clawdbotatg/clawd-pico-case/renders/plan/photo-stick-tilt.png

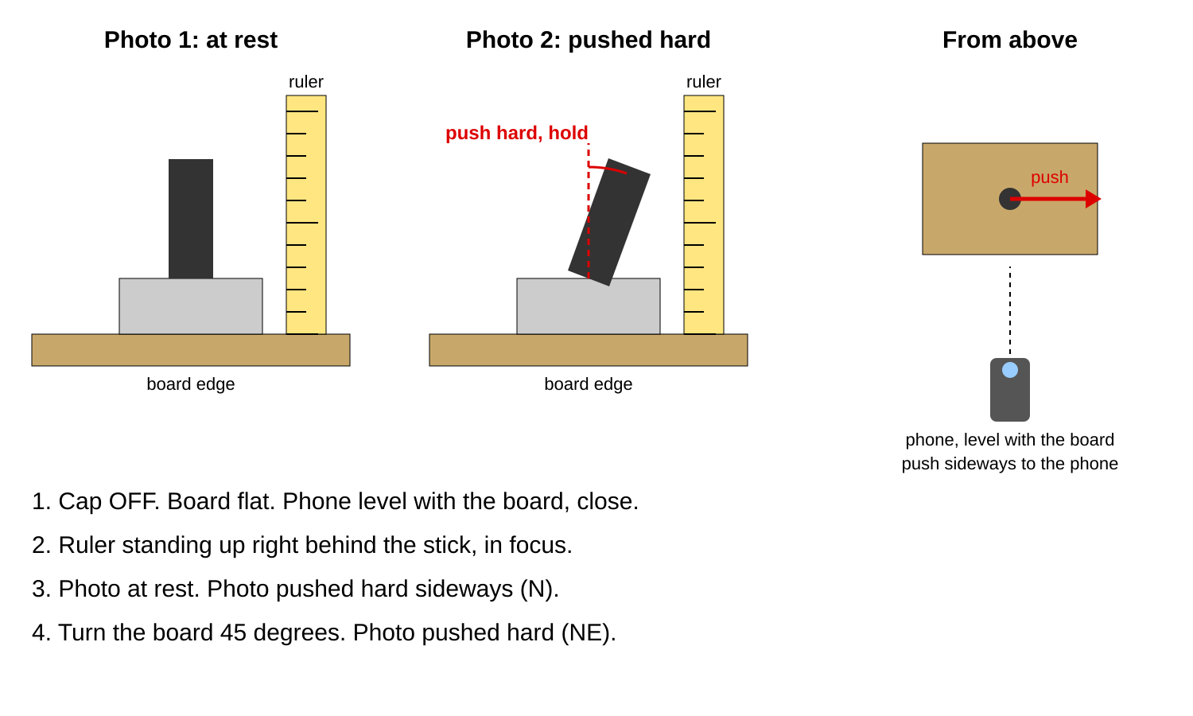
renders/plan/photo-stick-tilt.png
