clawdbotatg/clawd-pico-case/renders/r4-preview.png

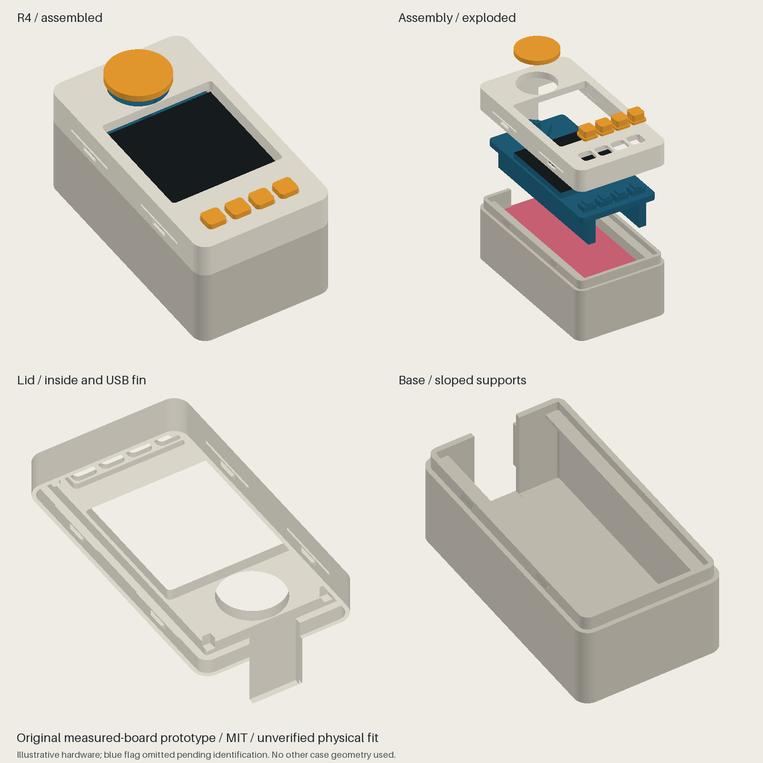
renders/r4-preview.png
