clawdbotatg/clawd-pico-case/renders/v3-browser.png

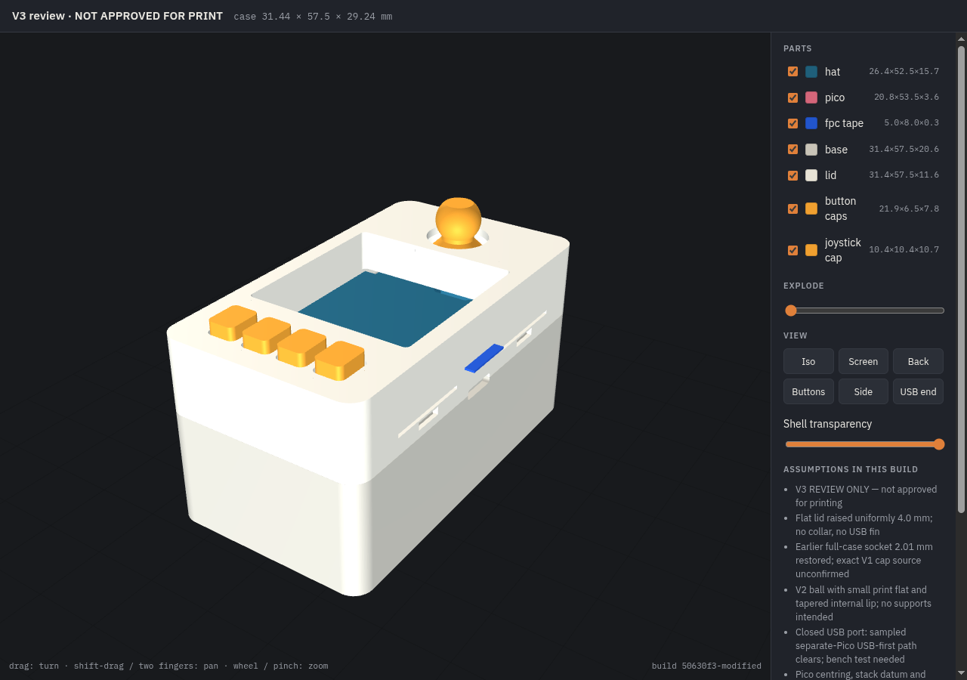
renders/v3-browser.png
