clawdbotatg/clawd-pico-case/renders/v3-low/browser.png

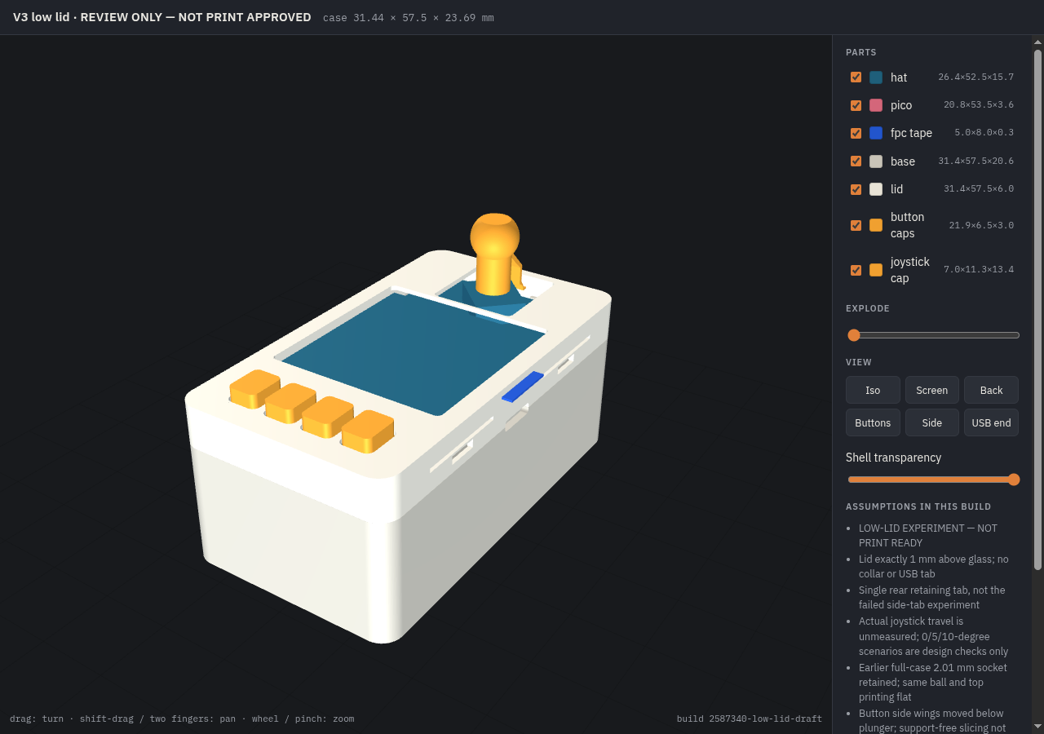
renders/v3-low/browser.png
