clawdbotatg/clawd-pico-case/stl/s2-tight-base/s2-base-and-four-buttons.stl

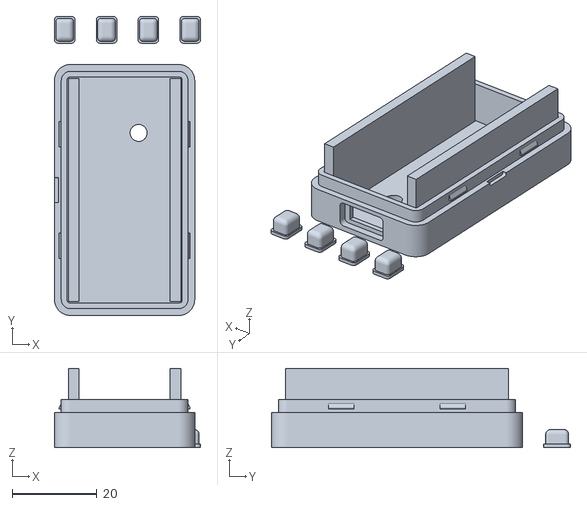
[picture p18: CAD file, 2026-09-25]
stl/s2-tight-base/s2-base-and-four-buttons.stl
34.4 x 70.4 x 18.7
