clawdbotatg/clawd-pico-case/stl/test/j24-fit/joystick-j24-fit-3.stl

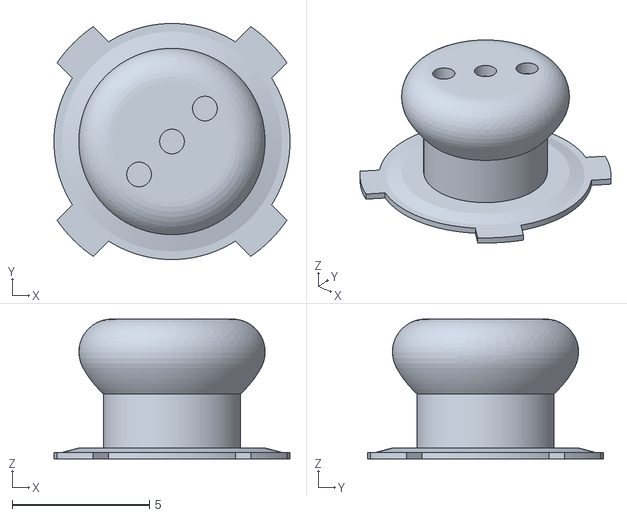
[picture p20: CAD file, 2026-10-02]
stl/test/j24-fit/joystick-j24-fit-3.stl
8.60 x 8.60 x 5.10
