clawdbotatg/clawd-pico-case/stl/test/j24/joystick-j24-B.stl

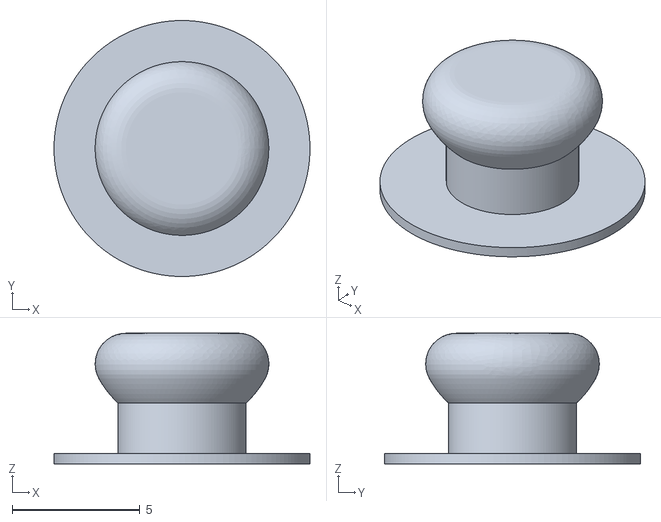
[picture p21: CAD file, 2026-10-02]
stl/test/j24/joystick-j24-B.stl
10.0 x 10.00 x 5.10
