clawdbotatg/clawd-pico-case/stl/test/v1.9/lid-v1.9-test-face-down.stl

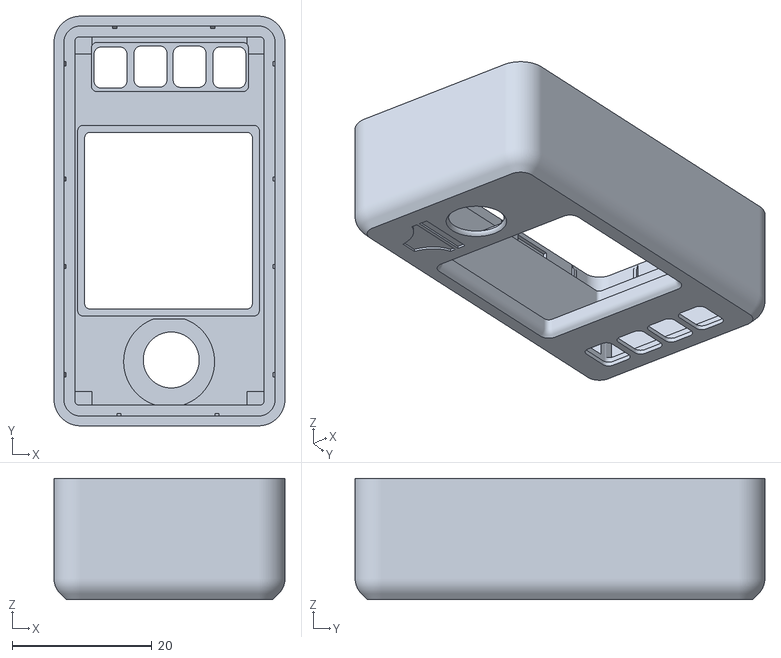
[picture p22: CAD file, 2026-10-02]
stl/test/v1.9/lid-v1.9-test-face-down.stl
33.0 x 58.6 x 17.4
