clawdbotatg/clawd-pico-case/stl/v3-flat/v3-flat-lid-face-down.stl

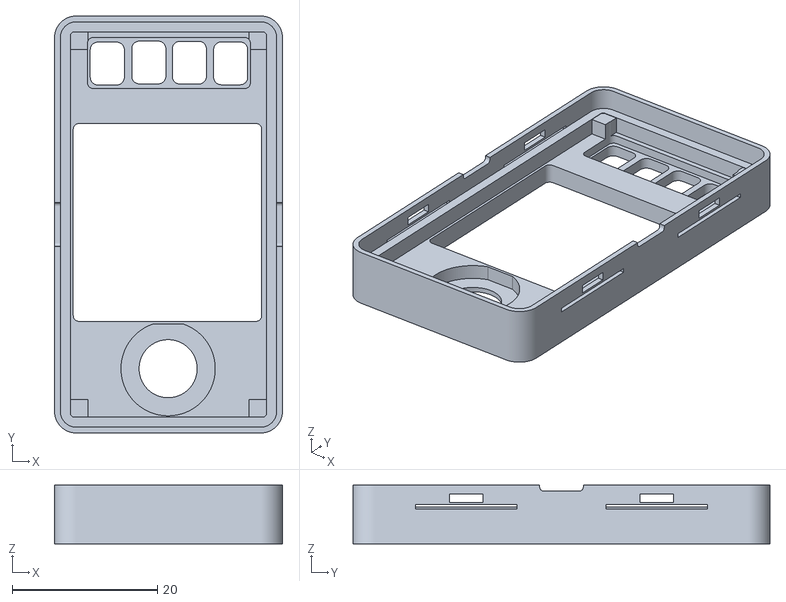
[picture p23: CAD file, 2026-09-25]
stl/v3-flat/v3-flat-lid-face-down.stl
31.4 x 57.5 x 8.10
