clawdbotatg/clawd-pico-case/stl/button_caps.stl

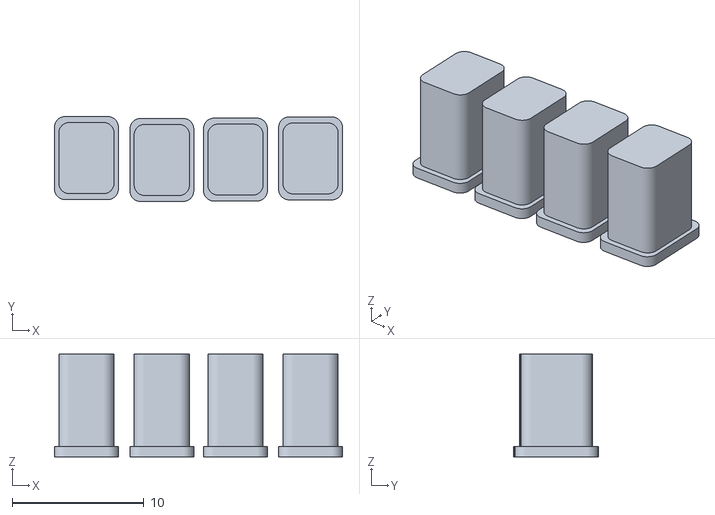
[picture p24: CAD file, 2026-09-25]
stl/button_caps.stl
21.9 x 6.44 x 7.79
