clawdbotatg/clawd-pico-case/stl/current/joystick.stl

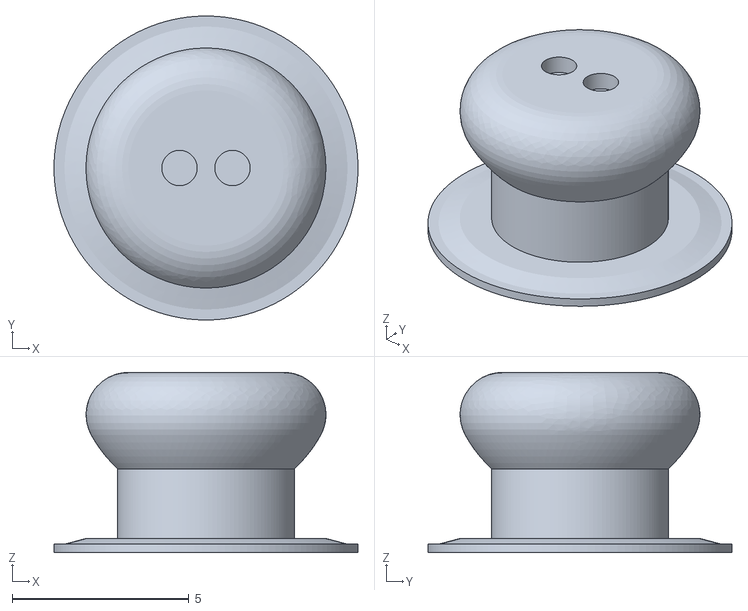
[picture p25: CAD file, 2026-09-30]
stl/current/joystick.stl
8.60 x 8.60 x 5.10
