clawdbotatg/clawd-pico-case/stl/j3-low-lid/lid-and-joystick.stl

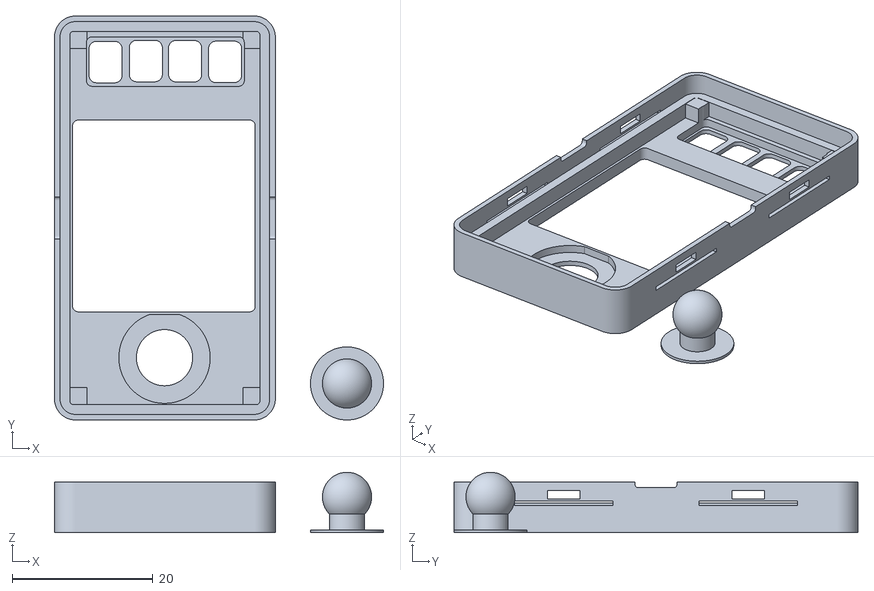
[picture p26: CAD file, 2026-09-25]
stl/j3-low-lid/lid-and-joystick.stl
46.8 x 57.5 x 8.60
