clawdbotatg/clawd-pico-case/stl/joystick-j1/joystick-cap.stl

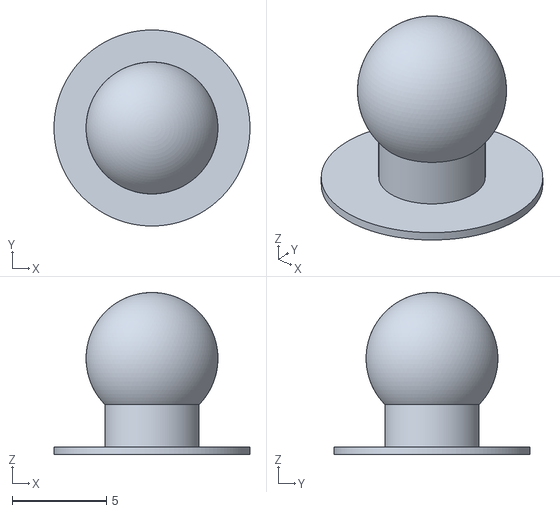
[picture p27: CAD file, 2026-09-25]
stl/joystick-j1/joystick-cap.stl
10.4 x 10.4 x 8.60
