clawdbotatg/clawd-pico-case/stl/l2-j2/l2-lid-and-j2.stl

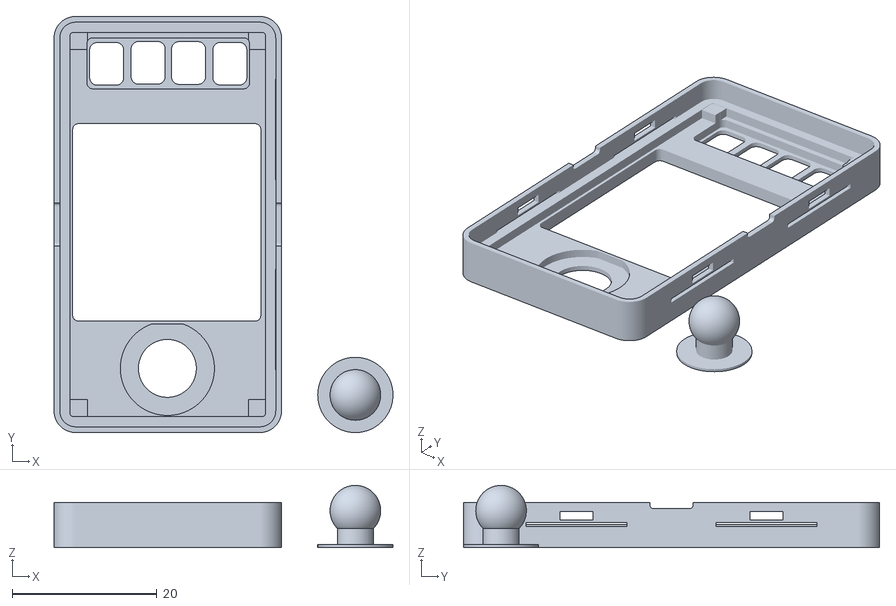
[picture p28: CAD file, 2026-09-25]
stl/l2-j2/l2-lid-and-j2.stl
46.8 x 57.5 x 8.60
