clawdbotatg/clawd-pico-case/stl/s1-full-print/button-1.stl

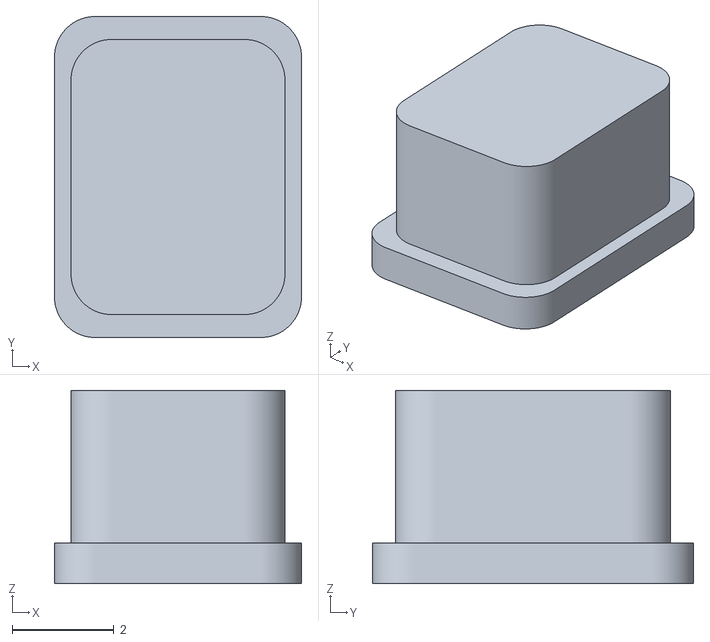
[picture p29: CAD file, 2026-09-25]
stl/s1-full-print/button-1.stl
4.85 x 6.30 x 3.79
