clawdbotatg/clawd-pico-case/stl/test/j24-fit/joystick-j24-fit-plate.stl

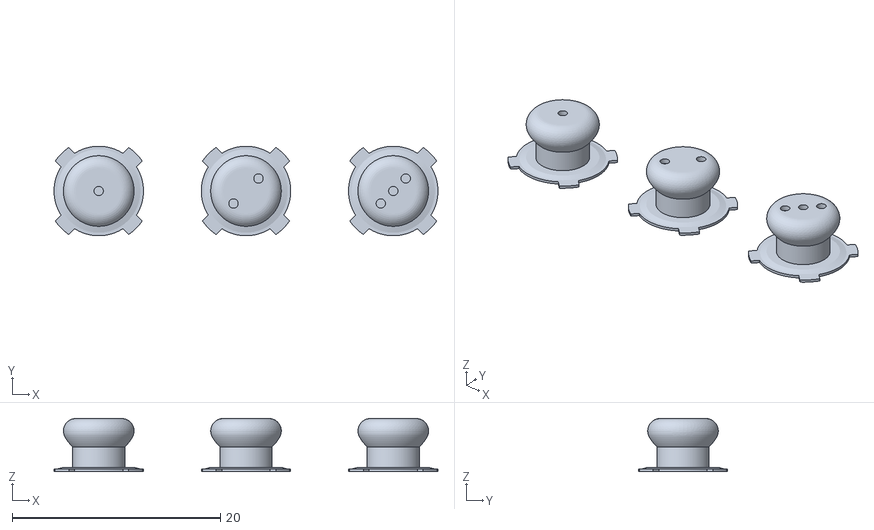
[picture p31: CAD file, 2026-10-02]
stl/test/j24-fit/joystick-j24-fit-plate.stl
36.9 x 8.60 x 5.10
