clawdbotatg/clawd-pico-case/stl/test/v1.9/logo-inlay-face-down.stl

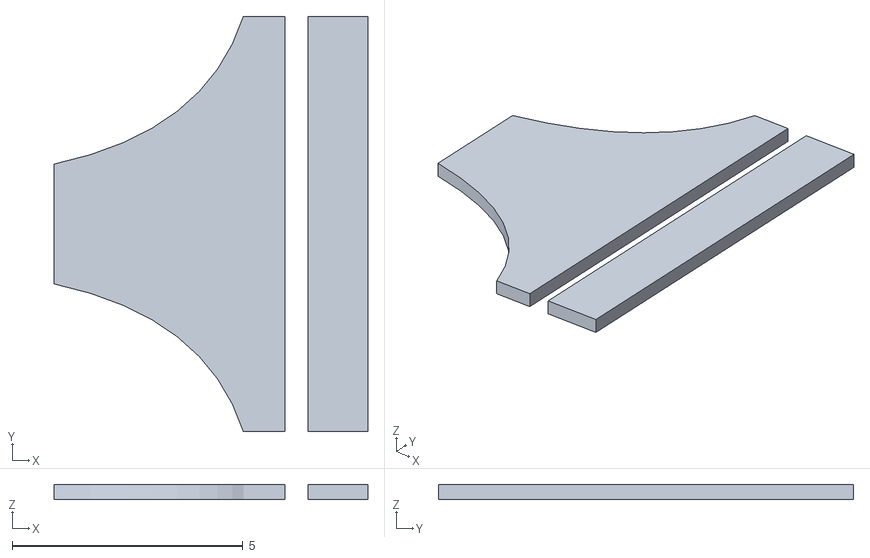
[picture p32: CAD file, 2026-10-02]
stl/test/v1.9/logo-inlay-face-down.stl
6.80 x 9.00 x 0.32
