clawdbotatg/clawd-pico-case/stl/base.stl

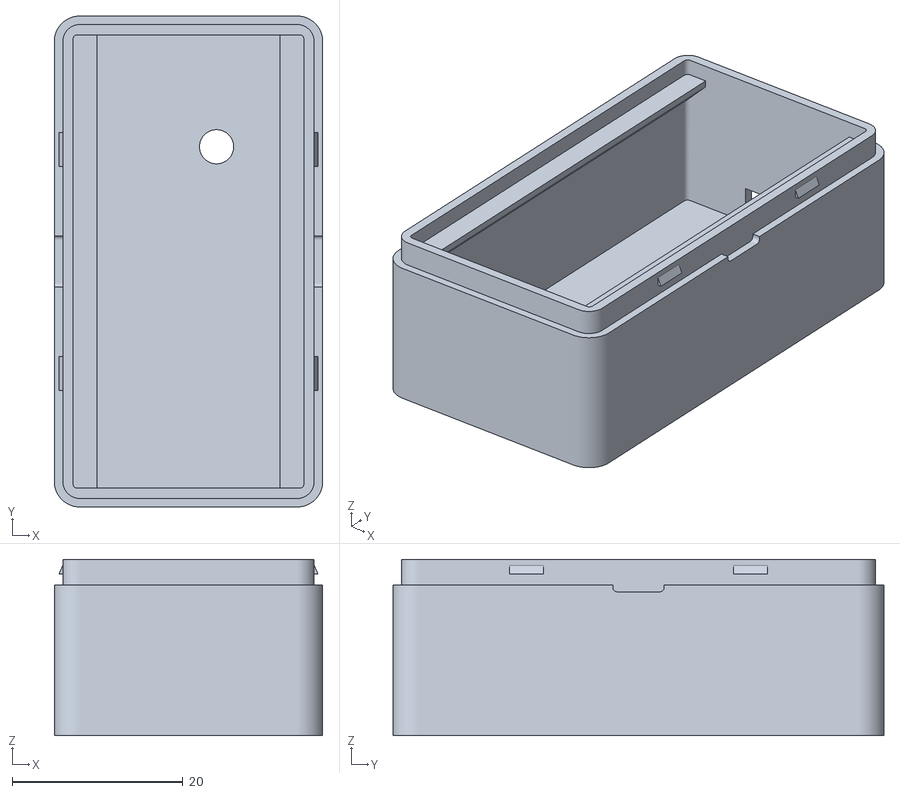
[picture p33: CAD file, 2026-09-25]
stl/base.stl
31.4 x 57.5 x 20.6
