clawdbotatg/clawd-pico-case/stl/current/lid.stl

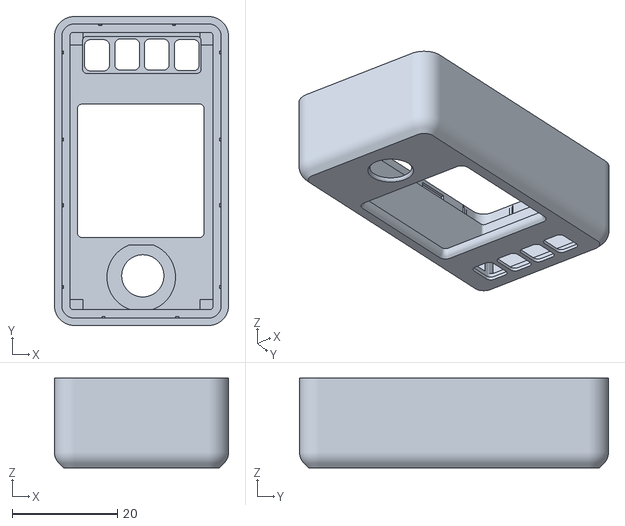
[picture p34: CAD file, 2026-09-27]
stl/current/lid.stl
33.0 x 58.6 x 17.1
