clawdbotatg/clawd-pico-case/stl/j3-low-lid/joystick-j3.stl

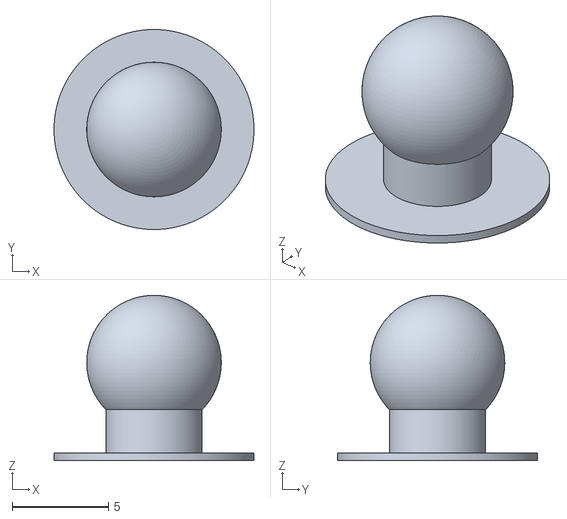
[picture p35: CAD file, 2026-09-25]
stl/j3-low-lid/joystick-j3.stl
10.4 x 10.4 x 8.60
