clawdbotatg/clawd-pico-case/stl/joystick-j1/lid-gauge.stl

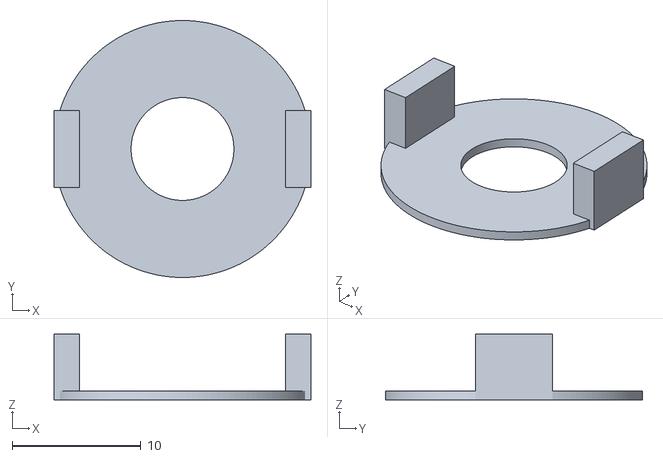
[picture p36: CAD file, 2026-09-25]
stl/joystick-j1/lid-gauge.stl
20.0 x 20.0 x 5.10
