clawdbotatg/clawd-pico-case/stl/test/aw-reset-v3/reset-v3-3-notch.stl

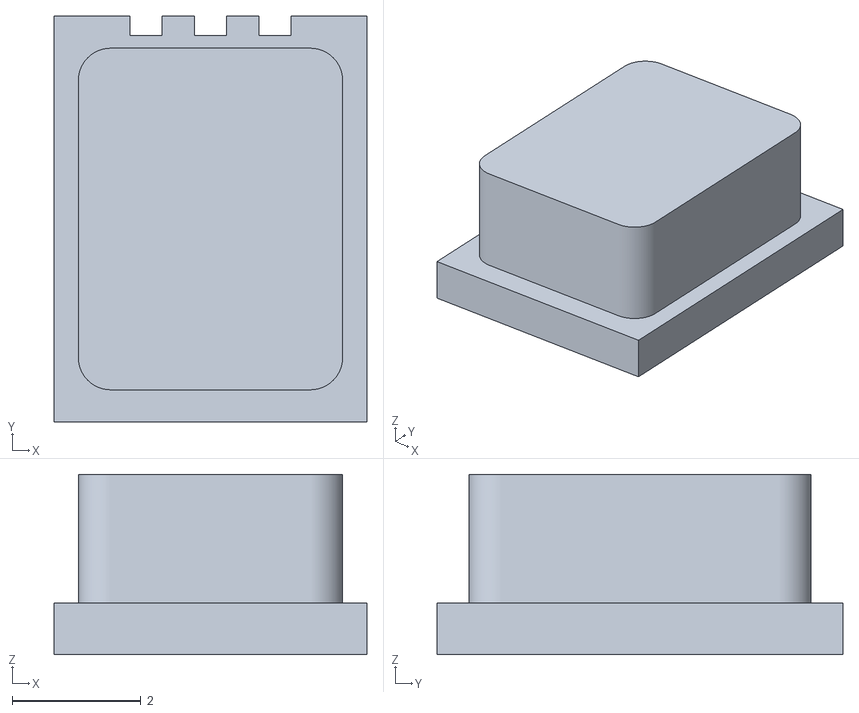
[picture p37: CAD file, 2026-10-09]
stl/test/aw-reset-v3/reset-v3-3-notch.stl
4.85 x 6.30 x 2.80
