clawdbotatg/clawd-pico-case/stl/v3-fit/v3-shells-only.stl

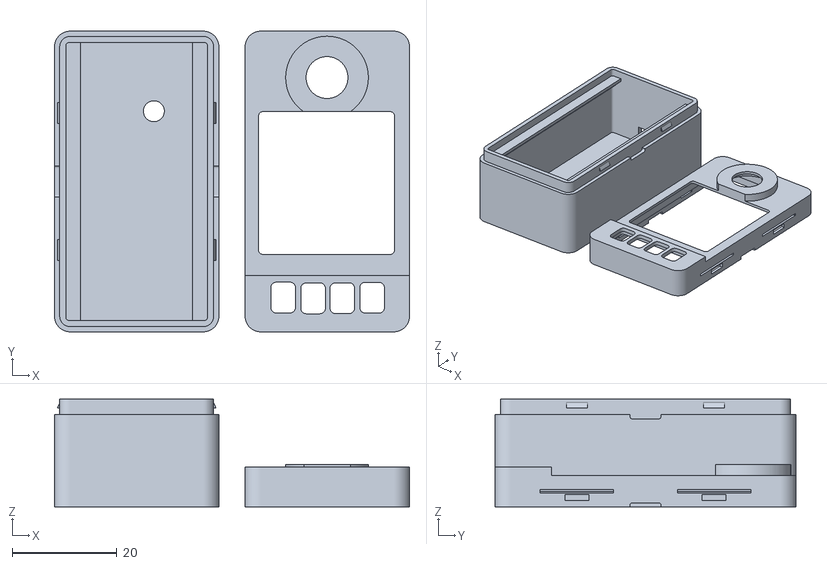
[picture p38: CAD file, 2026-09-25]
stl/v3-fit/v3-shells-only.stl
67.9 x 57.5 x 20.6
