clawdbotatg/clawd-pico-case/stl/current/button.stl

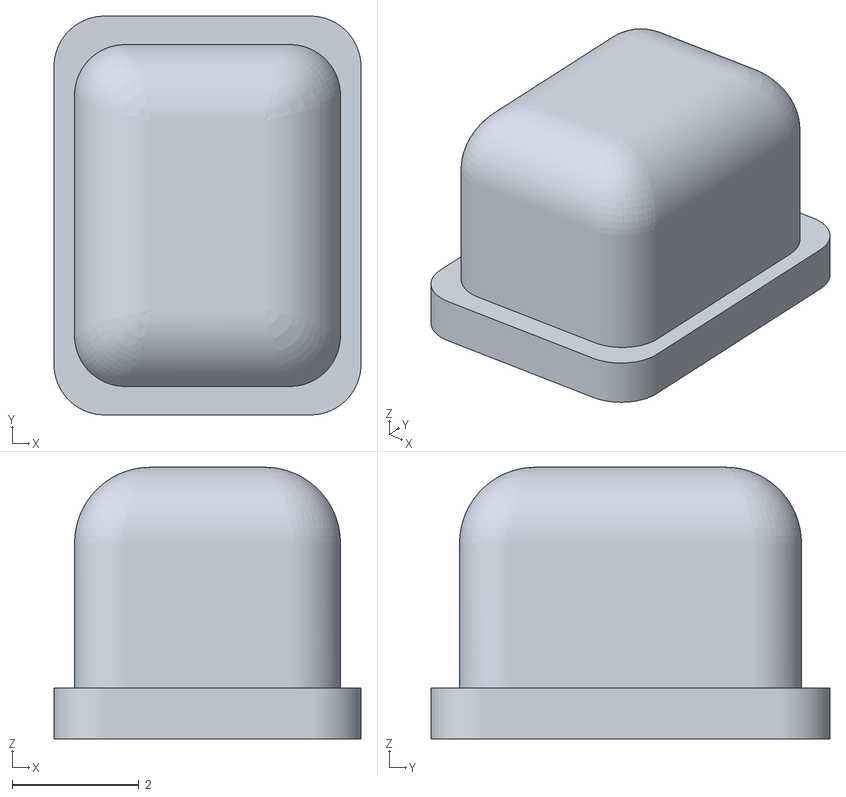
[picture p39: CAD file, 2026-09-25]
stl/current/button.stl
4.85 x 6.30 x 4.29
