clawdbotatg/clawd-pico-case/stl/lid.stl

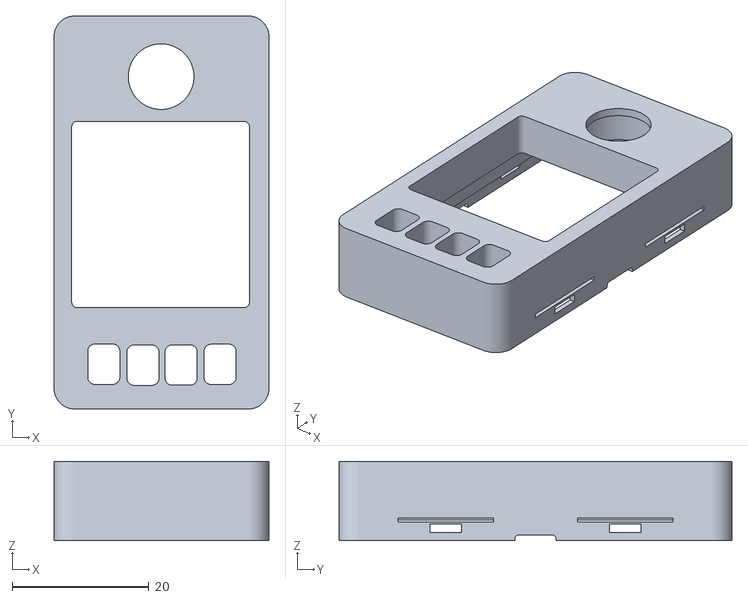
[picture p40: CAD file, 2026-09-25]
stl/lid.stl
31.4 x 57.5 x 11.6
