clawdbotatg/clawd-pico-case/stl/pico.stl

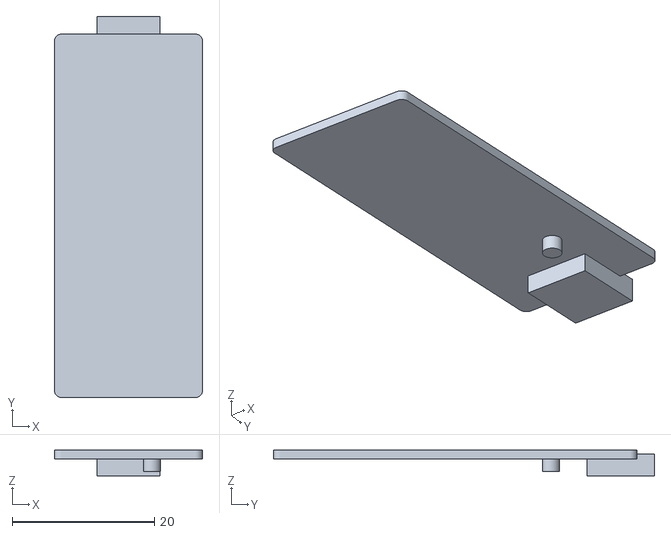
[picture p41: CAD file, 2026-09-25]
stl/pico.stl
20.8 x 53.5 x 3.64
