clawdbotatg/clawd-pico-case/stl/hat.stl

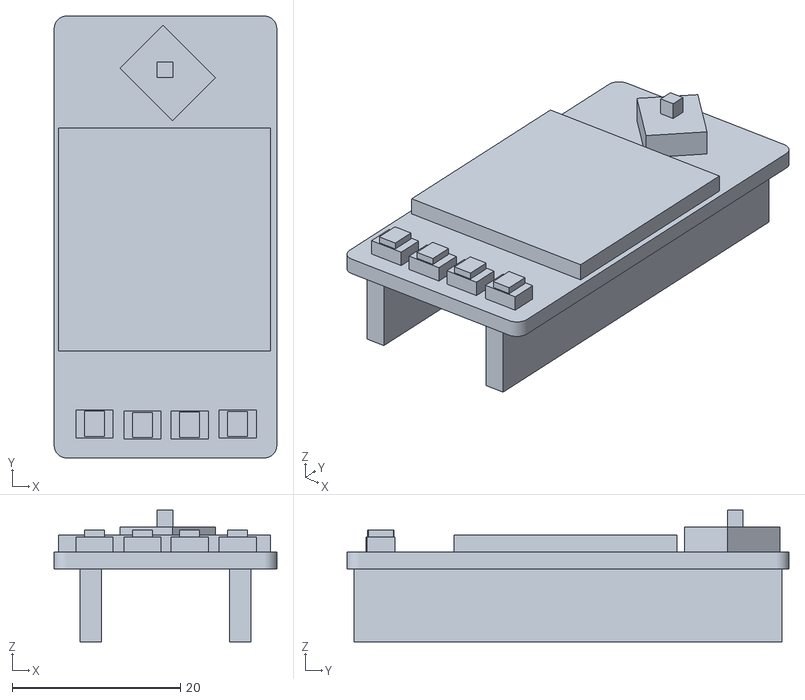
[picture p42: CAD file, 2026-09-25]
stl/hat.stl
26.4 x 52.5 x 15.7
