clawdbotatg/clawd-pico-case/stl/fpc_tape.stl

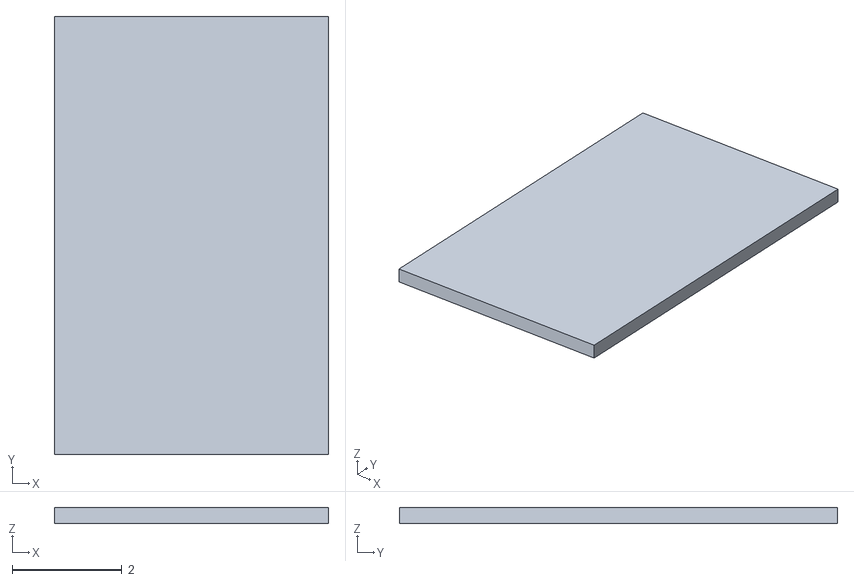
[picture p43: CAD file, 2026-09-25]
stl/fpc_tape.stl
5.00 x 8.00 x 0.3
