clawdbotatg/clawd-pico-case/prints/2026-09-25-v1.3-lid-petg.md

# v1.3 lid — white PETG

Austin approves the short-USB-end approach ("this is the way") and asks for
the lid in white PETG (bay 2). It replaces the v1.1 lip lid. The lid's USB-C
end wall is 0.5 mm further in, and there is no lip.

Source ccf3351, `stl/v1.3/lid-face-down.stl`, SHA256
`eddf98bfa6c56df3ee43523b8e432f1ef07ad944e9342fcf71011e93c7d7c223`.
33.04 × 58.60 × 16.56 mm. PETG, 0.16 mm, 4 walls, no supports, no raft,
face down.

Sent to the HTTP inbox as `20260925-205019-lid-face-down` with a GO (queue
after any running job). Status: new. Print start unconfirmed.

The lid matches only the v1.3 base: the case ends are 0.5 mm shorter, so it
will not sit flush on a v1.0 or v1.1 base.
