clawdbotatg/clawd-pico-case/prints/2026-09-25-v1.0-caps-petg.md

# v1.0 joystick + two buttons — gray PETG

Austin asks for the joystick cap and two button caps only, in gray PETG from
AMS bay 3. The parts are unchanged v1.0 (J2 joystick, S2 buttons 1–2; all
four buttons are identical). `cad/v1_caps_plate.py` lays them out.

File `stl/v1.0/v1.0-joystick-and-two-buttons.stl`, SHA256
`be922982d110cce2e86359edca736fd24d92bfe1885c461e6eff6b5294474495`.
30.10 × 10.40 × 8.60 mm. PETG, 0.16 mm, 4 walls, no supports, no raft,
flanges down.

Sent to the HTTP inbox as `20260925-190845-v1.0-joystick-and-two-buttons` with
an explicit GO (queue after any running job). Status: new. Print start
unconfirmed.
