clawdbotatg/clawd-pico-case/prints/2026-09-25-s2-base-buttons.md

# S2 replacement base + four buttons

Austin requests next iteration for tighter S1 closure and more distinct
rounded/taller buttons; minimize shell reprints. Print FIVE pieces only.
Keep existing S1 lid and J2 joystick. No change to case height/hole alignment.

File stl/s2-tight-base/s2-base-and-four-buttons.stl. Base floor DOWN/cavity UP,
four buttons flange DOWN. PLA available color,0.16mm,4walls, supports OFF,
raft OFF. No lid/joystick/PETG or extra parts.

New flat catch underside has short0.50mm overhang: inspect slicing along with
USB bridge, rails and rounded cap tops. Hold/report if support-free printing
is not viable; no silent geometry/orientation/support changes. Confirm bed
clear by camera, wait if busy, start watcher. Let plate cool before removal.

36 checks pass: same lid, base changes only at catches, seated clearance,
reduced nominal play, button interfaces/travel/retention and five-part plate.
Fit/force untested. Try closing gently, then hold by top and check for hanging
base or rattle. Test button feel/full travel and pry-notch release; do not
force if fit is too tight.0.04mm nominal play is not an FDM accuracy claim.

Source cc52b45 sent via HTTP inbox as
`20260925-161927-s2-base-and-four-buttons`.
Server confirms34.40×70.40×18.67mm, fits bed, matching SHA256:
`044036e3313a87cc659227e269e47603cd21a9ca204dde046f40b6c65acd14ca`.
Explicit GO accepted; initial status new, actual start unconfirmed.
Austin notified by inbox. Browser render/controls test also passed.

## Result

Printed and assembled with the S1 lid and J2. Austin: "This works. This is
good." The snap and the button feel are accepted. Three 0.25 mm nudges
remain (joystick hole, USB-C height, reset hole); they went into
[V1.0](../RELEASE-v1.0.md) and were not reprinted in PLA.
