clawdbotatg/clawd-pico-case/prints/2026-09-25-s1-full-case.md

# S1 full case — 2026-09-25

Austin approved interactive model and explicitly requested full set now.
Seven pieces: S1 lid/base, one unchanged J2 joystick, four unchanged V2
buttons. Approved S1 shell source 5c6f7ab. Original review artifacts retained.

Plate stl/s1-full-print/s1-full-case-seven-parts.stl. Individual STLs beside it.
Lid exterior FACE DOWN, base floor DOWN/cavity UP, all caps flange DOWN.
PLA available color, 0.16 mm, 4 walls for stronger shells, supports OFF,
raft OFF. No extra parts, no scaling or alternate orientations.

Operator must preview all seven pieces, thin control roofs, hidden catches,
USB bridge, support rails and cap sockets. Confirm bed clear by camera,
wait if busy, start print watcher. Hold/report if support-free slicing fails;
do not add supports or flip lid. Strength/joint force/physical fit untested.
Cool plate before removal; test assembly gently without forcing hardware.

Sent packaging source d57302f via HTTP inbox:
`20260925-145729-s1-full-case-seven-parts`.
Server confirms 71.08 × 74.50 × 18.67 mm, fits bed, matching SHA256
`185554416fa7e59e3f17f83e36e086e3585ead93e732c9803bf214de4090b9d1`.
14 packaging checks pass, including exact shell/J2 file matches, seven solids,
all parts on bed and separated. Explicit GO accepted; initial status new.
Austin notified by inbox. Actual print start not yet confirmed.
## User-supplied production photograph

Austin subsequently supplies IMG_0839 showing shells and controls on printer
bed. Archived with provenance/hashes at [s1-photos](s1-photos/README.md).
This supports physical production of the iteration; no exact completion time,
successful assembly, or functional fit is inferred from the photograph.
## Assembled fit feedback

Austin reports S1 very close. Holding top lets base hang approximately 0.25 mm;
closure too easy/loose. Buttons feel indistinct/close under finger. Requests
one-half reprint if possible and taller rounded button tops. Assembled photo
IMG_0840 archived in s1-photos, duplicate uploads saved once. Next S2 trial
keeps lid/J2 and replaces base catches plus four button tops.
