clawdbotatg/clawd-pico-case/prints/2026-09-25-l3-shifted-hole.md

# L3 — lid only alignment correction

Restore L1 face z4.20 and joystick underside z3.50 after L2 closure failure.
Only opening moves 1.00 mm toward LCD, diameter stays 8 mm. Pocket unchanged.
Reuse existing base/buttons/J2. User-owned IMG_0831/0830/0829 provide direction;
amount follows explicit request. No physical fit guarantee.

Print stl/l3-shifted-hole/l3-lid-face-down.stl, one lid FACE DOWN as exported.
PLA available color, 0.16 mm, 3 walls, supports OFF, raft OFF. No other parts.
Operator previews thin roofs/snap bridges, confirms bed clear by camera,
waits if busy and starts watcher. No orientation changes or added supports.
Source e082ac8 sent via HTTP inbox: `20260925-140900-l3-lid-face-down`.
Server confirms 31.44 × 57.50 × 7.20 mm, fits bed, matching SHA256
`36425a396bdc524a374d7511813842214572617c2d0387cb5ad942edbf78c358`.
Explicit GO accepted; initial status new. Print start unconfirmed.
Nine geometry checks and browser interaction test passed. Austin notified
by inbox. No physical fit result yet.
## Physical feedback

Austin reports 1 mm shift overshot; IMG_0833 latest versus IMG_0832 prior.
Next trial should move halfway back and slightly photo-up.
