clawdbotatg/clawd-pico-case/prints/2026-09-25-l2-j2.md

# L2 lid and unchanged J2 — 2026-09-25

Austin explicitly authorizes this uncertain-fit trial. L1 roof and underside
lowered 1.00 mm with thickness retained; unchanged mating skirt, base, buttons.
J2 joystick reprint byte-identical, not rejected J3.

File stl/l2-j2/l2-lid-and-j2.stl. Exactly one lid FACE DOWN and one joystick
flange DOWN, socket mouth at bed. PLA available color, 0.16 mm, 3 walls,
supports OFF, raft OFF. No other parts. Inspect bridges, thin roof, socket and
flange in slicer; camera-confirm bed clear, wait if busy, start watcher.

Seven structural checks pass. Hat/button CAD overlaps explicitly recorded
in renders/l2-j2/validation.json. Physical fit is NOT confirmed; user requests
the print anyway. Test gently, never force the lid onto hardware.

Sent source c7a0315 via HTTP inbox as `20260925-133723-l2-lid-and-j2`.
Server confirms 46.84 × 57.50 × 8.60 mm, fits bed, matching SHA256:
`7777ba5cc1b18bc5eb67cdedb275aa89db74edf8472d4698a71c1621fcf4f692`.
Explicit GO accepted. Initial status new; print start not confirmed.
Austin notified by inbox. No physical fit result yet.
## Physical feedback

Austin reports case will not close with joystick and buttons installed.
L2 rejected; restore L1 height for next lid. Keep J2 joystick.
