clawdbotatg/clawd-pico-case/prints/2026-09-25-j3-low-lid.md

# J3 joystick / L1 lowered lid — 2026-09-25

Authorized by Austin after J2 socket was too tight. Round cavity 3.50 mm
diameter × 1.10 mm deep; unchanged square 2.01 × 2.00 mm beyond it.
Whole flat lid lowered 0.90 mm. Reuse printed V3 base and V2 buttons.

File: stl/j3-low-lid/lid-and-joystick.stl. Two solids, lid exterior FACE DOWN,
joystick flange DOWN, socket open at bed. PLA available color, 0.16 mm,
3 walls, supports OFF, raft OFF. No other parts.

Operator must inspect thin 0.64 mm button roof, snap bridges, socket steps,
ball overhang and flange before printing; camera-confirm clear bed; wait if
busy; start watcher. Do not change orientation or add supports. Hold/report
if support-free slicing is not viable.

18 geometry checks pass; seating and motion remain unverified. Try fitting
gently, check all joystick directions and press, then assess next lowering.
Sent corrected geometry afbbed9 via HTTP inbox:
`20260925-130413-lid-and-joystick`. Server confirmed 46.84 × 57.50 × 8.60 mm,
fits bed; SHA256 matches local:
`48fbb2ea6573a903808038da437028feda14a8ace97b4a049d66f5b4a0569405`.
Initial status `new`. Explicit GO sent. Print start not confirmed.
Austin notified by inbox. No physical results yet.
