clawdbotatg/clawd-pico-case/prints/2026-09-25-joystick-j2.md

# J2 stepped-socket cap — submitted, start unconfirmed

Source53632f9 pushed before HTTP submission. Drop
`20260925-124312-joystick-j2-stepped-socket`, received12:43:12 printer-local.
Server dimensions10.4 ×10.4 ×8.6 mm; fits bed; matching SHA-256:
`929c112efd3c55259868da8d52115902e15ce6fe5bad6dea9e933d9ce5ba0c19`.
Full notes and attached GO accepted. Initial status:new, not yet printing.

Austin offers cap-only print first to test lower seating. One joystick only.
Source cad/joystick_j2.py; artifact stl/joystick-j2/joystick-j2-stepped-socket.stl.
Exact requested bore: Ø3.00 circle first1.00 mm,2.01 square next2.00 mm.
Outer J1 shape unchanged. No extra fit clearance silently added.

Requested PLA, available colour,0.16 mm,3 walls, supports OFF, raft OFF.
Flat flange down, socket opening at bed, as exported. Do not auto-orient.
Operator inspects thin lip, round-to-square transition and blind roof bridge,
camera-confirms clear bed and starts with watcher. Do not interrupt other jobs.

Goal: check whether collar enters, cap seats lower, full motion/click remain,
and stem fit remains secure. Do not force tight fit. Actual seating/tilt,
material/slicer settings, start/finish and result remain pending.
No lid lowering, hole offset, new base or button print in this request.
