clawdbotatg/clawd-pico-case/prints/2026-09-25-v3-base.md

# V3 base only — submitted, start unconfirmed

Austin reports the corrected flat-face lid looks great and requests the
matching V3 base. This is unchanged geometry from commitb4548b3, paired in
the validation with flat lid145e386. No new design or cap/lid reprint.

File: stl/v3-fit/base.stl
SHA-256: aa332d86b061bd1323c2ae3ca81942a583ab0b8826c398b58744be395370f4db
Drop:20260925-113816-base, received2026-09-25T11:38:16 printer-local.
Server dimensions31.44 ×57.50 ×20.64 mm; fits bed; manifest/server hashes
match. Initial status:new. Attached GO request accepted through HTTP inbox.

Requested one copy, PLA, available colour,0.16 mm,3 walls. Base exterior
bottom DOWN, cavity UP as exported; no auto-orientation, supports or raft.
Inspect USB bridge and snap features, camera-confirm clear bed, then start
with watcher. No older files authorized. No SSH/direct printer control.

Closed V2-position USB aperture, reset access, pry recesses and original
snap geometry retained. Actual slice/start/finish/fit and snap force pending.
Assemble USB-first, then LCD; test lid closure gently and do not force it.
