clawdbotatg/clawd-pico-case/prints/2026-09-25-v3-flat.md

# V3-FLAT lid-only correction — submitted, start unconfirmed

Physical feedback update: Austin reports the lid looks great and requests
the matching V3 base. Printed lid therefore confirmed by user, but snap fit
and complete assembly are not yet established. Original dispatch below.

Dispatch2026-09-25T11:15:49 printer-local, source145e386 pushed first.
Drop `20260925-111549-v3-flat-lid-face-down`, initial status `new`.
Server dimensions31.44 ×57.50 ×8.10 mm, fits bed. SHA-256 verified:
`b159a9e3d0240a77e1e7594c756f781f342fc97a2b4f45b0cac01550dccc3801`.
Full orientation/support constraints accepted; attached GO request accepted.
Lid face-down contact934.2166 square mm. Browser preview/controls verified.
No direct start or camera observation here; operator handles preflight/start.

Austin explicitly requests flat whole face raised as needed, printed FACE
DOWN, no supports. All facez5.1, joystick retaining ceilingz4.4 unchanged.
This supersedes upright lid job20260925-103637-v3-shells-only (on hold after
failed stopped print). Server accepted message not to restart the old lid.

Print exactly one file: stl/v3-flat/v3-flat-lid-face-down.stl.
No buttons, joystick, gauge or base. Existing V2 buttons and J1 cap unchanged.
V3 base geometry unchanged; previous server history says base not printed.

Orientation already baked into STL: flat exterior face atbedz0, inside up.
Do not flip or auto-orient. Requested PLA, available colour,0.16 mm,3 walls,
supports OFF, raft OFF, no peel-off layer. Operator checks slice, especially
snap-slot bridges, camera-confirmed clear bed and then starts with watcher.

699 required CAD checks pass; closed manifold mesh; all outer positive-Z
horizontal faces coplanar in assembly. Existing buttons1.3 mm proud at rest,
.92 at full press. Screen depth3.05 mm expressly accepted for this iteration.
Inherited J1 movement uncertainty retained. Actual rigid fit still untested.

Review: ../JOYSTICK-REVIEW.md. Build: .venv/bin/python cad/v3_flat.py.
Actual slice/settings/start/finish and physical test pending.
