clawdbotatg/clawd-pico-case/prints/2026-09-25-v3-fit.md

# V3 fitted shells — submitted, print start unconfirmed

## Subsequent server report — superseded

At11:13 on2026-09-25, inbox history reports Austin instructed LID ONLY:
printing began10:57:20, base NOT printed. At11:10:14 job was put on hold
after Austin stopped it at layer34/50 (stop11:09), reporting failure.
Actual supports-off settings per operator note: PLA A1,0.16,3 walls.
Underlying slicer preview not inspected locally. Failed print not success.

Austin rejects upright orientation and authorizes a flat whole face printed
face-down. Attached message asks operator to retain old job on HOLD, never
restart old lid. New correction is recorded in2026-09-25-v3-flat.md.

## Dispatch — 2026-09-25 10:36:37 printer-local

Source commit b4548b3, pushed before submission. HTTP health confirmed.
Drop `20260925-103637-v3-shells-only`, server status `new`.
Combined size67.88 ×57.50 ×20.64 mm, fits bed. Server hash matches below.
Complete notes accepted untruncated using multipart form-string fields.
Attached GO message accepted, conditional on successful support-free slice
review and camera-confirmed clearance. No SSH or direct printer control.
The server handles Telegram notifications. Request accepted, not confirmed
printing; actual slice/start/finish remains unverified.

Austin requests new closed-port base and full lid, no new buttons/joystick.
Complete review: ../JOYSTICK-REVIEW.md. Original MIT geometry.

Send stl/v3-fit/v3-shells-only.stl: exactly two solids, base and lid.
SHA-256:6e2ccf73749eb8d4e11a80c02acddf9d81427033e541a0764dd93d77d432abc3
Reuse physically printed prototype-v2 buttons and joystick-j1 cap.

Requested PLA, available colour,0.16 mm,3 walls, one copy. Both shells
upright as exported: base floor down, lid skirt down. No supports, raft or
extra peel-off layer. Do not auto-orient, flip, scale or modify geometry.

Mandatory operator slice review: upright lid ceilings around buttons and
joystick hole, thin front wall, corner pad overhangs,14 mm snap slot bridges,
skirt adhesion and9.57 mm USB opening bridge. HOLD if supports/raft needed.
Inspect bed/camera and wait for other work to finish; do not interrupt it.

697 required CAD checks pass; inherited J1 motion contacts remain disclosed.
User reports J1 full hand-held movement, not yet rigid-lid fit. V2 buttons and
USB bounds independently compared; cap file unchanged. Browser checks pass.
This is a prototype, not proven physical fit or verified support-free slicing.

Actual material/settings, slicer preview, duration, start/finish, socket and
snap fit, USB-first assembly, button motion and joystick fit remain pending.
