clawdbotatg/clawd-pico-case/prints/2026-09-25-joystick-j1.md

# J1 isolated joystick test — submitted, start unconfirmed

User authorized after disclosure of known10-degree binding scenario.
Source6bec71a; original MIT geometry. Only cap and small lid gauge.
Full design/evidence/bench checklist: ../JOYSTICK-REVIEW.md.

File: stl/joystick-j1/two-part-test.stl
SHA-256:67aefeda6ba8ab3cb511a0a668318bb95e532de43e1d31005674da7ab3e38f43
Drop:20260925-100248-two-part-test; received2026-09-25T10:02:48 printer-local.
Server dimensions35.4 ×19.99 ×8.6 mm; fits bed; hash matches.

Requested: one copy (two parts), PLA, available colour,0.16 mm,3 walls,
supports disabled, raft disabled. Preserve upright cap flange-down and
inverted gauge top-down; no scaling/auto-orientation.

Full follow-up message explicitly asks operator to print after slice review
and camera-confirmed clear bed, without interrupting another job. Initial
multipart notes were truncated at a semicolon; full requirements were sent
in the attached JSON message, including HOLD rather than add supports/raft.

Review thin0.4 mm lip,2.01 mm socket roof bridge, ball overhang and feet.
Known16/96 motion collisions at unpressed10 degrees disclosed to operator.
No geometric changes to hide failures. No SSH or direct printer control.

Initial status:new. Actual slicing, preview, material, duration, start,
completion and fit results pending. Inbox submission is not print start.
