clawdbotatg/clawd-pico-case/prints/2026-09-24-v2.md

# V2 / R5 — printed; physical fit failed

Additional2026-09-25 feedback: USB alignment is good, but the long lid tab
closing the base's USB channel leaves unwanted gaps. Austin wants V1-style
closed base port at the corrected position. V3 must remove that tab.

Update 2026-09-25: Austin reports the physical result. Pry access, bottom
button-hole alignment and rectangular cap shape worked. Joystick does not
fit the PCB stick; raised collar/support layer caused problems, including
button openings. Do not reprint unchanged. See
[V2 review and correction goals](../reports/2026-09-25-v2-review.md).
Dispatch notes below preserve what was known at submission; actual slicer
settings, toolpaths and completion time remain unverified.

Original first-principles MIT case; follows Austin's V1 feedback.
Source tag: prototype-v2. All five requested changes implemented:
captive ball joystick, pry notches, higher/tighter USB opening, wider/taller
rectangular buttons, scan-positioned bottom button access.

Requested profile: PLA, loaded colour acceptable, 0.16 layer, P2S0.4 nozzle,
textured PEI. Seven pieces from four files. Separate button solids.
Keep export orientations. Support inverted lid face beneath raised collar;
review cap flange/ball supports, block socket, inspect bridges and lid fin.
Do not use incomplete tag r5-wip-joystick-pry or the old R4 drops.

Actual profile, slicer preview, duration, G-code hash and start/finish state:
pending. No physical result yet.

Local checks: 276 geometry checks passed; seven print/sample meshes checked
for closed edges, no duplicate-vertex triangles and bed z=0. All source and
artifact SHA-256 hashes match stl/manifest.json. Pre-commit git label in the
manifest is resolved by exact source hashes, not a claim of a clean parent.

## Acceptance

- Joystick installs before lid; flange remains inside; full free return,
  directions and centre/tilted clicks; stays engaged when pulled gently.
- All rectangular caps slide independently, retain and stand taller.
- Notches admit plastic tool; snaps release without damage.
- USB cable fully seats; tighter/higher opening does not load connector.
- Bottom hole is centred on intended button; safe toothpick access.
- No board preload, solder contact, rattle or unintended inputs.
- Inspect support removal damage and snap fatigue across repeated openings.

Blue flag identity and unmeasured components remain unresolved; see REPORT.md.

## Dispatch — 2026-09-24 21:31 printer-local time

HTTP inbox health verified. Uploaded four files from tag prototype-v2,
commit f278436. Server hashes match the saved manifest; all fit the bed.

| Part | Drop ID | Size mm | Returned status |
|---|---|---|---|
| Base | 20260924-213135-v2-base | 31.44 × 57.50 × 20.64 | new |
| Lid | 20260924-213135-v2-lid | 31.44 × 57.50 × 22.47 | new |
| Four buttons | 20260924-213136-v2-button_caps | 21.86 × 6.44 × 3.79 | new |
| Joystick | 20260924-213136-v2-joystick_cap | 10.40 × 10.40 × 11.10 | new |

SHA-256 respectively:

- c5323202cb799232d58f8dd2d748c174cb9ab4595e717888c039f04c93744c7d
- 84bc1748ae2f8b5e0330dd4a3c3035bad73612e4e0d23cd9d014a1ab816672d7
- eddd8851f76464792617cc2507e38900152abb0eca94ae870dc7e12ced72c1fa
- 04513f67bb3f3dcdfad140e2c0f176f729c1e3c79b9f8609b7fd618531655110

Grouping message accepted: print these seven pieces on one plate next,
after current job and camera-confirmed clearance. Requested PLA0.16, loaded
colour acceptable, explicit lid/cap support review and socket support blocker.
Reiterated hold/supersede for all four old R4 IDs, not any running job.
Inbox sends Austin Telegram notifications. Submission is not a print start.
No SSH, direct printer start, stop or interruption was used.
