clawdbotatg/clawd-pico-case/prints/2026-09-24-v1-feedback.md

# V1 — Austin's first-principles case print

2026-09-24. Source: Austin's hands-on feedback and three supplied photos.
Austin identifies this as V1, built from first principles without using
another licensed case. Repo license remains MIT. Exact printed CAD commit,
slicer settings and material are unconfirmed; plastic appears yellow/orange.
Do not equate V1 with the internal R4 revision without evidence.

Austin: "Most other things are good about the case."

## Requested changes

1. **Joystick:** mount on the board before the lid. Retaining lip inside;
   shaft and smaller round ball protrude. Taller, less wide and flat.
2. **Opening:** small pry notch at the seam; case is too hard to take apart.
3. **USB-C:** connector sits higher than the hole. Shift opening toward
   lid and reduce excess space while preserving cable access. Photo shows
   extra space below the socket but provides no reliable millimetre offset.
   Check the actual printed revision/stack; do not overwrite caliper data
   with a perspective-photo estimate.
4. **Buttons:** wider rectangles, not squares; taller above the lid.
   Reduce top/bottom flange lips while retaining caps. Rectangular holes
   should make insertion orientation clear. Exact sizes remain design
   choices to check against button pitch, retention and travel.

Keep other features unless required clearance checks show a problem.

5. **Bottom button access:** Austin requests a hole directly over the pink
   board's button/pad, about its size, for a toothpick or thin tool without
   opening the case. Button identity (reset versus boot selection), centre
   position and pad dimensions must be confirmed from this actual board.
   Do not infer reset behaviour from the word Pico. Prefer a nonconductive
   tool; keep opening and tool path clear of adjacent components.

## Photos

- [Joystick, IMG_0801](v1-feedback/IMG_0801.jpg)
- [Buttons, IMG_0800](v1-feedback/IMG_0800.jpg)
- [USB-C, IMG_0799](v1-feedback/IMG_0799.jpg)

Original uploads respectively: paste-f2819d95-IMG_0801.jpg,
paste-f925a63a-IMG_0800.jpg, paste-42cd1b6f-IMG_0799.jpg.
Copied unchanged. Austin identifies these as his original V1 print;
they are not third-party case reference geometry.

## Work status

R5 draft implements captive ball joystick and two seam pry notches.
USB-C, rectangular/taller buttons and bottom button access remain pending. No physical fit,
opening-force or support success is claimed. Do not print this checkpoint.
Save subsequent changes as separate documented commits before dispatch.

## Follow-up: V2 candidate completed

Austin instructed using the existing pink-board scan, making a good estimate
and iterating, then sending the next case to print. All five requests are
now implemented in V2 / R5; earlier pending notes above record the checkpoint
state, not current state. See `2026-09-24-v2.md` for dispatch and testing.
Bottom-hole placement is estimated from scan01 with a reproducible script
and overlay; no further caliper measurement was required to make this trial.
