clawdbotatg/clawd-pico-case/prints/2026-09-25-v1.1-lid-petg.md

# v1.1 lid — white PETG (spacer test)

Austin asks for the v1.1 lid first, in white PETG from AMS bay 2, queued
after the print that is running now. It tests the USB-end lip, and he is not
sure it will work. It pairs with the PETG v1.0 base until a v1.1 base is
printed: the lip works on its own, and the base stops only help with locating.

Source 0b33543, `stl/v1.1/lid-face-down.stl`, SHA256
`ff261f9b66ad2356734524644bf6b8f7ca9224067e2acfdd572cedc7b0f36b27`.
33.04 × 59.10 × 16.56 mm. PETG, 0.16 mm, 4 walls, no supports, no raft,
face down.

Sent to the HTTP inbox as `20260925-195849-lid-face-down` with a queued GO.
Status: new. Print start unconfirmed.

Check: the lid closes without forcing the board, the board no longer slides
toward USB-C, and the joystick and buttons line up.

## Result

Austin reports that the lid finished printing. No fit result yet; he is
waiting for the v1.1 base.
Fit: the spacer is in the right place but too big, and the screen board
won't sit flush. Next is v1.2 with 0.5 mm.
