clawdbotatg/clawd-pico-case/prints/2026-09-25-v1.1-base-petg.md

# v1.1 base — black PETG (spacer test)

Austin asks for the v1.1 base after the white v1.1 lid finished. He gave no
colour, so it uses black PETG from AMS bay 1, the same as the v1.0 base. It
adds the two rail end stops at the USB end.

Source 0b33543, `stl/v1.1/base-floor-down.stl`, SHA256
`0e3683f0ea0cdc54a15284d3276b2ea02231a642810b9b950b6caa1d64ac587f`.
33.04 × 59.10 × 20.34 mm. PETG, 0.16 mm, 4 walls, no supports, no raft,
floor down.

Sent to the HTTP inbox as `20260925-203651-base-floor-down` with an explicit
GO. Status: new. Print start unconfirmed.
