clawdbotatg/clawd-pico-case/prints/2026-09-25-v1.0-lid-petg.md

# v1.0 lid — white PETG

Austin asks for the v1.0 lid only, in white PETG from AMS bay 2. This is the
first print of the joystick-hole nudge (0.25 mm away from the LCD, toward
USB-C). It pairs with the black PETG v1.0 base
(`2026-09-25-v1.0-base-petg.md`).

Source 5828eae (tag v1.0), `stl/v1.0/lid-face-down.stl`, SHA256
`5c8f3de2b1344a636c33000a765d98db39c47462dfe634202e86d9ed02a20109`.
33.04 × 59.10 × 16.56 mm, fits bed. PETG, 0.16 mm, 4 walls, no supports,
no raft, exterior face down, one copy.

Sent to the HTTP inbox as `20260925-183007-lid-face-down` with an explicit GO
(queue after the base if that is still printing). Status: new. Print start
unconfirmed.

Check: the joystick cap is centred in its hole, the snap onto the PETG base
is tight, and the buttons move freely.

## Result

The PETG set (black base, white lid, gray caps) works well. The boards slide
about 1.2 mm along the case and line up best pushed toward the buttons. The
fix is in V1.1 (USB-end spacer).
