clawdbotatg/clawd-pico-case/prints/2026-09-25-v1.0-base-petg.md

# v1.0 base — first PETG print

Austin asks for the v1.0 base only, in black PETG from AMS bay 1. This is the
first print of the reset-hole and USB-C nudges and the first PETG print of
the design. It fits the existing S1 lid.

Source 5828eae (tag v1.0), `stl/v1.0/base-floor-down.stl`, SHA256
`46c5d4744dbc07998bad362fbae040c7a4b581de4d05d3520b044f64440a10ad`.
33.04 × 59.10 × 18.67 mm, fits bed. PETG, 0.16 mm, 4 walls, no supports,
no raft, floor down, one copy.

Sent to the HTTP inbox as `20260925-174202-base-floor-down` with an explicit
GO. Status: new. Print start unconfirmed.

Check: snap tightness in PETG vs PLA S2, reset button reachable through the
moved hole, USB-C plug seats with the raised opening.
