clawdbotatg/clawd-pico-case/prints/v1-feedback/IMG_0799.jpg

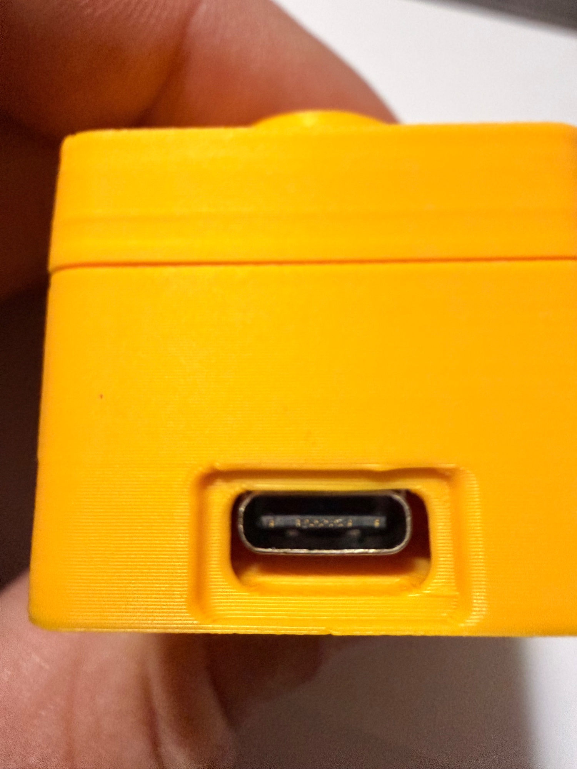
prints/v1-feedback/IMG_0799.jpg
