clawdbotatg/clawd-pico-case/prints/v3-photos/IMG_0817.jpg

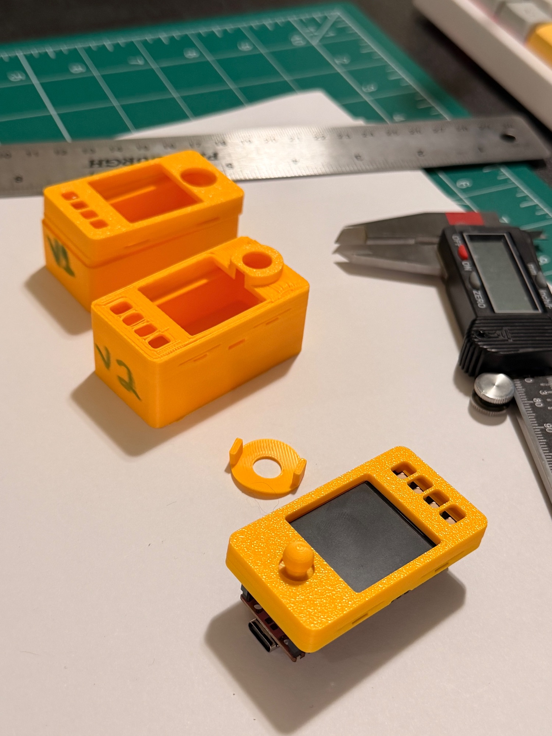
prints/v3-photos/IMG_0817.jpg
