clawdbotatg/clawd-pico-case/prints/v3-photos/IMG_0822.jpg

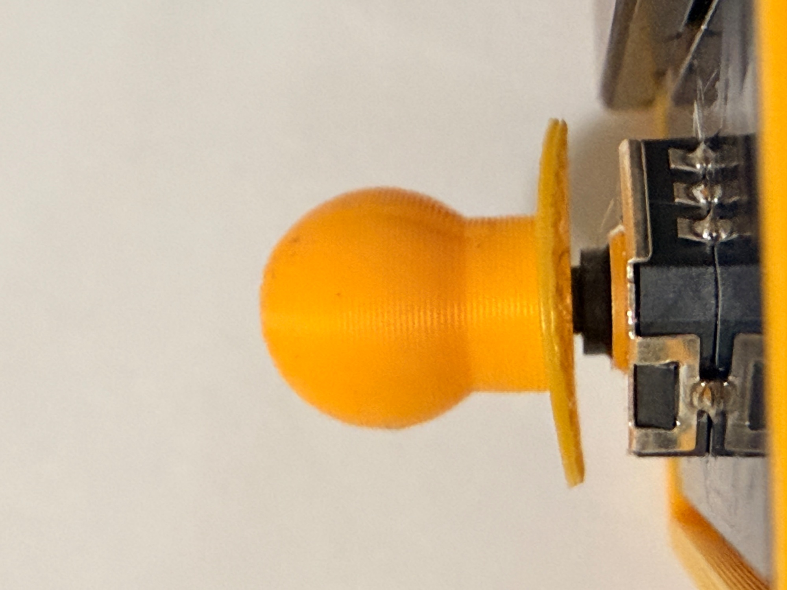
prints/v3-photos/IMG_0822.jpg
