clawdbotatg/clawd-pico-case/prints/v3-photos/IMG_0827.jpg

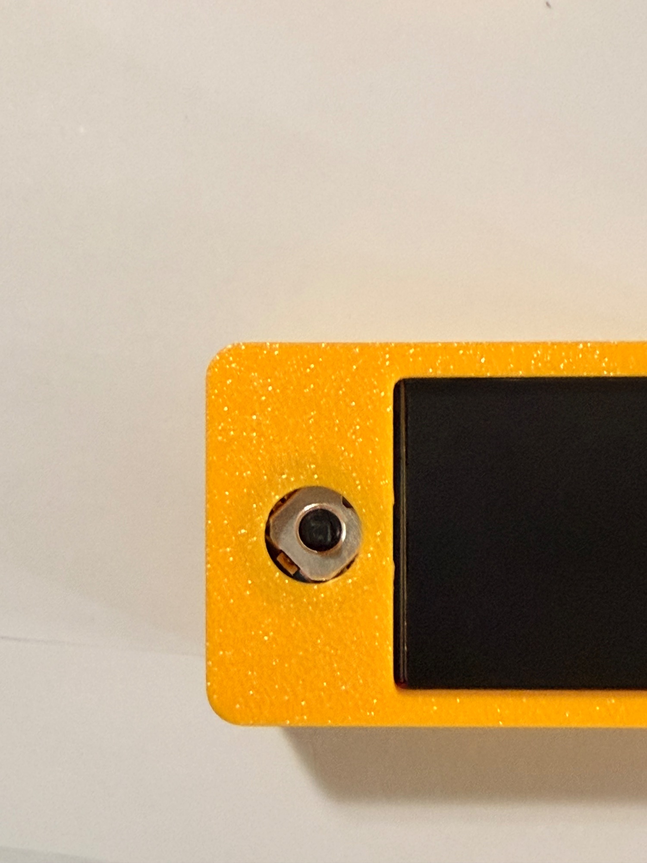
prints/v3-photos/IMG_0827.jpg
