clawdbotatg/clawd-pico-case/prints/2026-09-24-test3-r4.md

# Test 3 / R4 — submitted to inbox; print start unconfirmed

Purpose: verify corrected mating fit, flexible latch bands, vertical USB
insertion channel and lid fin, four PCB pads, shelves, caps and cable access.
Source: commit `eb892ee`, annotated tag `prototype-r4`, exact hashes in
stl/manifest.json. Copy that manifest with the plate when actually printing.
Base/lid must both be R4. Source, outputs and tag have been pushed to GitHub.

Proposed profile: Bambu P2S, 0.4 nozzle, grey PLA, 0.16 layer, textured PEI.
Inspect 14 mm bridges above latch bands and catch windows; supports/profile
are not validated. Base upright, lid/joystick inverted, buttons flange-down.
Separate button solids. See REPORT.md for assembly and careful snap release.

Optional joystick trial sockets: 1.86, 1.96, 2.06 across flats; default 1.91.
Keep samples identified; start with largest and do not force onto the stem.

| Test | Result |
|---|---|
| Blue flag identified / safe removal or clearance | Pending |
| No component/solder contact at shelves and four pads | Pending |
| Stack drops in, USB passes channel | Pending |
| Lid fin straight, slides into channel | Pending |
| Four snaps close/release without excessive force | Pending |
| Four independent button clicks/returns, inverted retention | Pending |
| Joystick full directions, centre/tilted click, cap retention | Pending |
| Cable fully inserts and maintains connection | Pending |
| Rattle, accidental presses, repeated opening damage | Pending |
| Slicer bridge result, first-layer expansion, material/profile | Pending |

Actual print time/material/profile and photos: not recorded.

## Dispatch attempt — 2026-09-24

Austin supplied the print-3d workflow and requested printing plus complete
GitHub iteration tracking. Read the skill; attempted the documented print-Mac
SSH connection. Authentication was denied, so the Mac's slicer/preflight
scripts could not be accessed. Requested the correct access method.

Direct printer camera succeeded: yellow parts occupy the plate. This is not
an R4 print. No R4 slicing, upload, start, pause or stop command was sent.
Actual filament/tray and finish state have not been queried. The proposed
grey PLA profile above is not a verified current material selection.

Next: restore print-Mac access, read its printing instructions, check live
status/camera/AMS, slice the tagged R4 files as one arranged plate, inspect
preview/bridges, and record verified profile, duration and G-code hash before
starting on a cleared plate. Retain the design tag unchanged.

## Corrected dispatch — 2026-09-24 20:59 printer-local time

The SSH dependency above was an agent mistake. The print-3d skill described
the Mac-local workflow, while the separate send-to-printer skill described
the existing LAN HTTP inbox. SSH is not required. Inbox health verified;
four R4 files uploaded and their returned SHA-256 hashes matched the saved
R4 manifest. All returned `fits_bed: true`.

| Part | Inbox ID | Size mm | Status at submission |
|---|---|---|---|
| Base | `20260924-205932-base` | 31.44 × 57.50 × 20.64 | new |
| Lid | `20260924-205932-lid` | 31.44 × 57.50 × 18.92 | new |
| Four button caps | `20260924-205933-button_caps` | 22.01 × 5.14 × 2.99 | new |
| Joystick cap | `20260924-205933-joystick_cap` | 14.00 × 14.00 × 4.11 | new |

Posted one grouping message requesting these four drops (seven pieces) on
one plate after the current job and plate clearance. Requested PLA, 0.16 mm,
grey preferred but loaded PLA color acceptable. Notes preserve exported
orientation, require separation of button solids, and flag lid bridges/fin
for slicer inspection. Optional joystick socket samples were not submitted.

The server's inbox notifications alert Austin. Submission is not a print
start. Actual slicing, settings, duration, G-code hash and fit result remain
pending. The print-3d library skill was updated and verified to put this
HTTP submission route first, explicitly requiring no SSH. No credentials
or private skill contents were added to this repository.

## Hold requested — 2026-09-24

After Austin rejected the externally installed joystick, all four drops
were still `new` when checked. Posted a general HTTP inbox message asking
the operator to hold/supersede those exact R4 IDs, preserve their history,
and leave any already running older job alone. Message accepted; operator
acknowledgment/status transition unconfirmed. R5 draft has not been sent.
