clawdbotatg/clawd-pico-case/prints/2026-09-24-test2-full-case.md

# 2026-09-24 test 2 — full case, best guess

- Purpose: first full fit. Base, lid v3, joystick cap v3, button caps.
- Source: `cad/` at commit 4010773, `stl/print/`.
- Changes vs test 1: snap windows + wedge bumps (test 1's notches removed
  nothing), joystick hole 12.0, neck + disc joystick cap, USB-C slot covers
  both stand-off readings, 1 mm plug recess (plug size guessed 12.5 x 7.0),
  two lid pads hold the LCD board down. Assumes the blue tab is peeled.
- Printer: Bambu Lab P2S, 0.4 nozzle, PLA grey, 0.16 mm, no supports, one plate.
- Sent: 19:18, drops `20260924-191852-base`, `-lid`, `-joystick_cap`, plus
  `20260924-184357-button_caps` (unchanged). Test 1 drops marked skip.
- Result: (fill in) what fit, what did not, photos.
