clawdbotatg/clawd-pico-case/prints/2026-09-24-test1-lid-caps.md

# 2026-09-24 test 1 — lid + button caps + joystick cap

- Purpose: check the lid against the real hat before printing the base:
  screen window, four square button holes (1.0 mm webs), joystick hole, cap
  fit (4.2 post in a 4.7 hole, 5.3 flange under the lid), snap notches.
- Source: `cad/` at commit 6469436, `stl/print/{lid,button_caps,joystick_cap}.stl`.
- Printer: Bambu Lab P2S, 0.4 nozzle, textured PEI. PLA. 0.16 mm. No supports;
  all parts exported flat-face-down (lid and joystick cap flipped).
- Sent: 18:43 to the print inbox as drops `20260924-184357-lid`,
  `-button_caps`, `-joystick_cap`, one message asking for one plate.
- Result: (fill in) what fit, what did not, photos.
- Note (audit, same evening): the lid in this drop has snap notches cut on the
  wrong side of the skirt. It still tests the window, holes and caps; not the snap.
