clawdbotatg/clawd-pico-case/prints/2026-10-01-v1.8-test.md

# V1.8 TEST plate (not the current version)

Two lids and two caps on one plate. stl/current is unchanged (v1.7 + J22).

- Lid +0.3: v1.7 lid 0.3 mm taller inside (the same stretch v1.5 used)
- Lid +0.5: 0.5 mm taller
- J23, 1 dot: J22 with tabs 2× J16 (was 1.55×), thin like J22
- J23, 2 dots: same tabs at full flange thickness (stiffer)

Bases are unchanged: use a printed v1.7 base.

Test each cap in each lid: hard pull stays in; NW/NE/SW/SE pushes never click
the centre; centre press clicks alone. Keep the shortest lid that works.

PETG 0.16, 4 walls, no supports, raft or brim. Lids face down (elephant-foot
compensation 0.15), caps flange down, away from the bed centre.

`stl/test/v1.8/v1.8-test-plate.stl`, SHA256 `3cb74574f930d11dba1e3956975c03d9e37c328e89c978193be141e5fafdaaa7` (server hash matches). Drop `20261001-190916-v1.8-test-plate`, no colour or GO.

## Result (Austin, 2026-10-01)

Lid +0.3 with the existing J22 joystick works pretty darn well. Next: V1.9 test.
