clawdbotatg/clawd-pico-case/measurements/2026-09-24-cal-B2-lcd-button-body-1.jpg

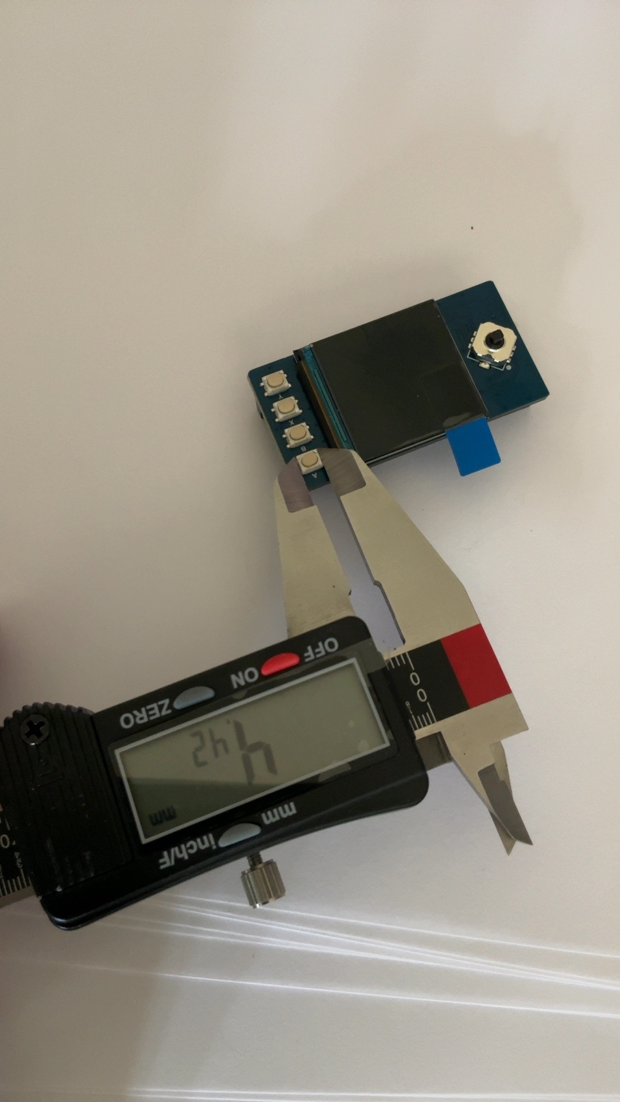
measurements/2026-09-24-cal-B2-lcd-button-body-1.jpg
