clawdbotatg/clawd-pico-case/measurements/2026-09-24-cal-B3-lcd-button-casing-height-1.jpg

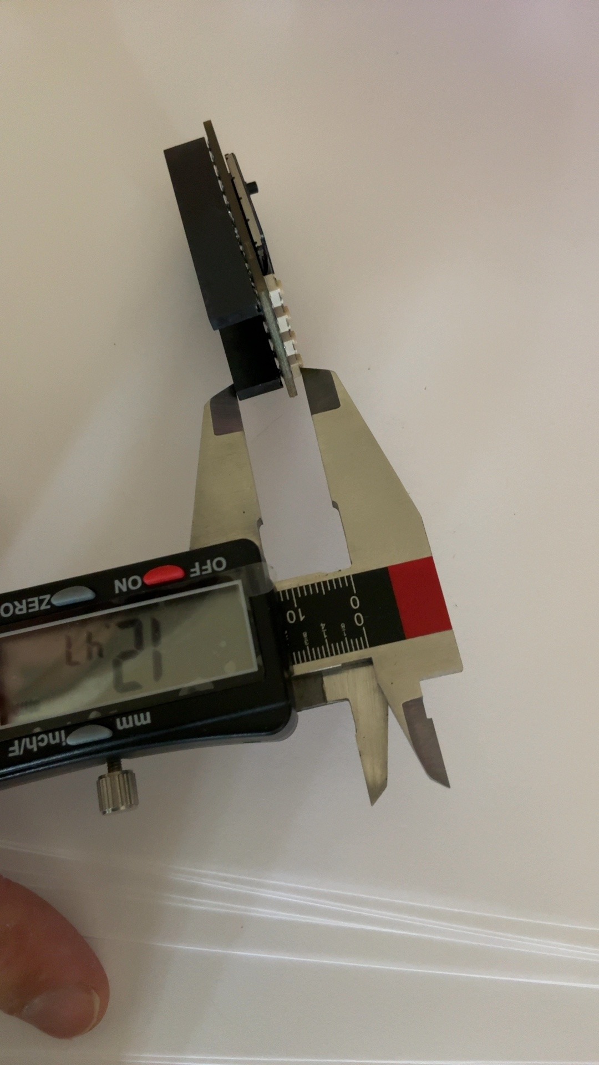
measurements/2026-09-24-cal-B3-lcd-button-casing-height-1.jpg
