clawdbotatg/clawd-pico-case/measurements/2026-09-24-cal-B4-lcd-plunger-long-1.jpg

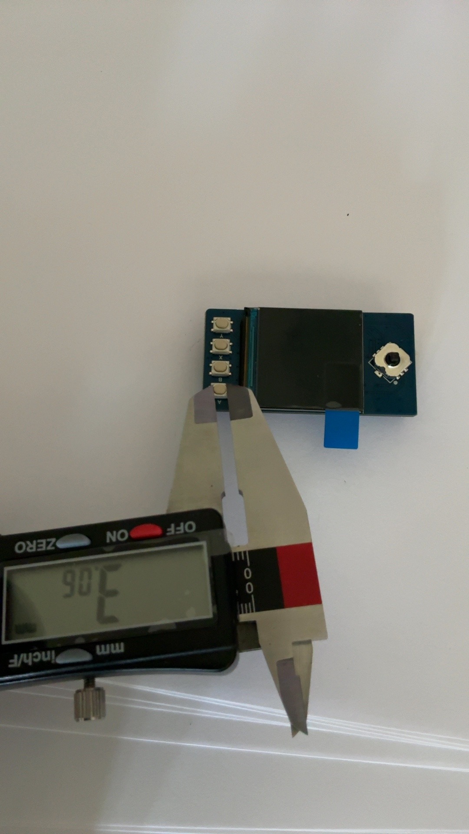
measurements/2026-09-24-cal-B4-lcd-plunger-long-1.jpg
