clawdbotatg/clawd-pico-case/measurements/2026-09-24-cal-B5-lcd-button-height-1.jpg

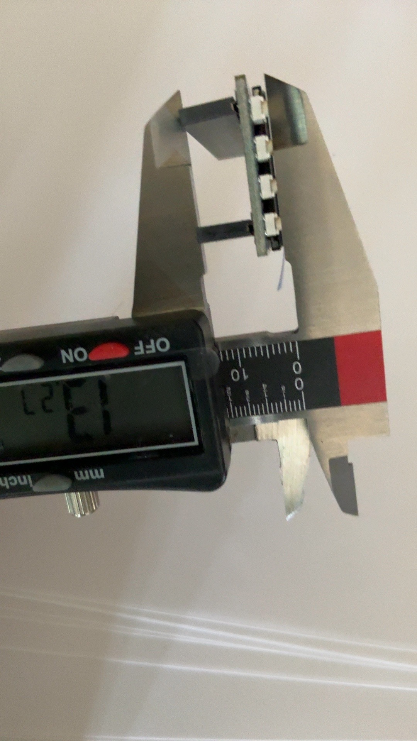
measurements/2026-09-24-cal-B5-lcd-button-height-1.jpg
