clawdbotatg/clawd-pico-case/measurements/2026-09-24-cal-B6-lcd-button-pressed-1.jpg

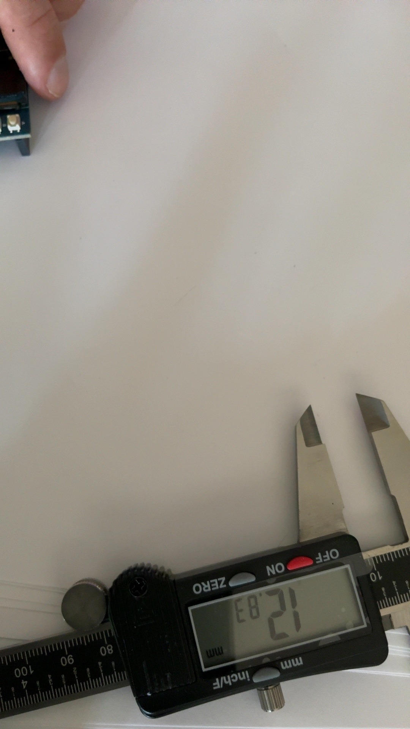
measurements/2026-09-24-cal-B6-lcd-button-pressed-1.jpg
