clawdbotatg/clawd-pico-case/measurements/2026-09-24-cal-J6-lcd-joystick-height-1.jpg

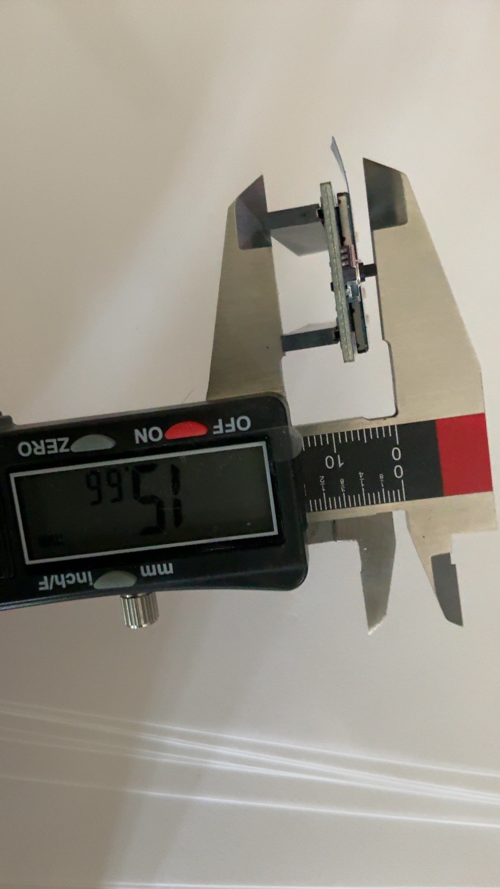
measurements/2026-09-24-cal-J6-lcd-joystick-height-1.jpg
