clawdbotatg/clawd-pico-case/measurements/2026-09-24-cal-L1-lcd-board-length-1.jpg

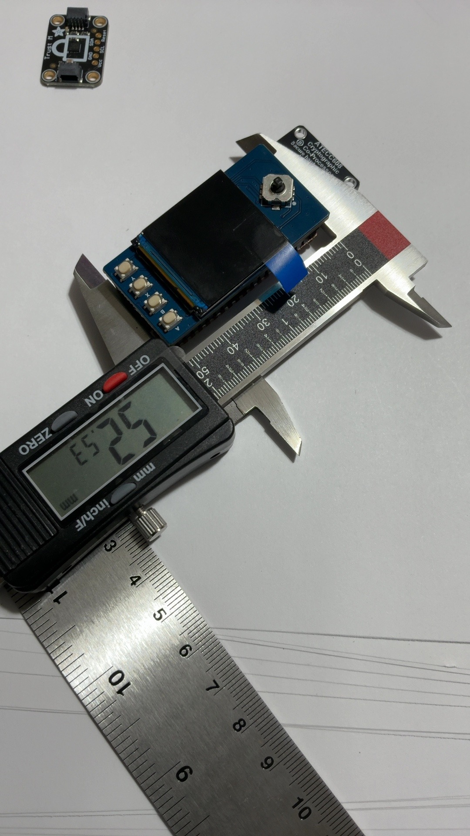
measurements/2026-09-24-cal-L1-lcd-board-length-1.jpg
