clawdbotatg/clawd-pico-case/measurements/2026-09-24-cal-L2-lcd-board-width-1.jpg

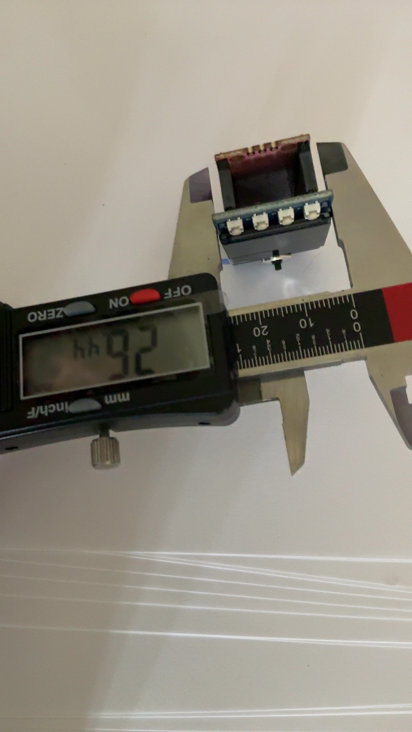
measurements/2026-09-24-cal-L2-lcd-board-width-1.jpg
