clawdbotatg/clawd-pico-case/measurements/2026-09-24-cal-L3-lcd-pcb-thickness-1.jpg

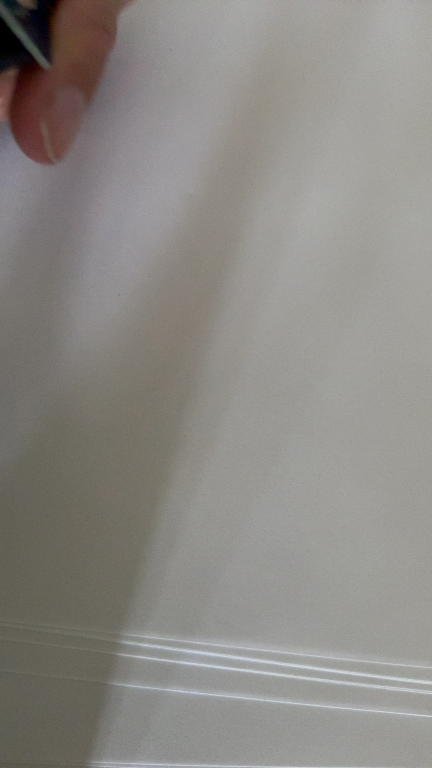
measurements/2026-09-24-cal-L3-lcd-pcb-thickness-1.jpg
