clawdbotatg/clawd-pico-case/measurements/2026-09-24-cal-L7-lcd-socket-height-1.jpg

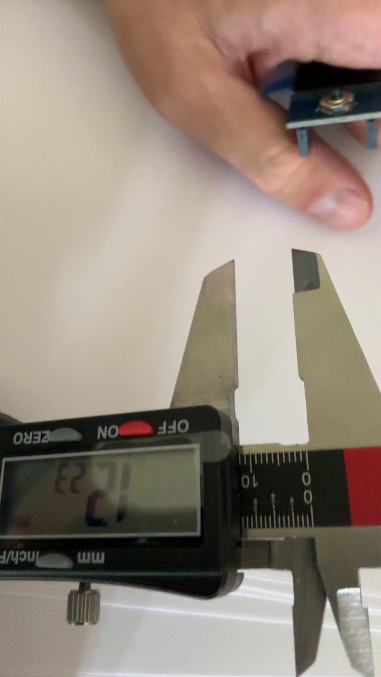
measurements/2026-09-24-cal-L7-lcd-socket-height-1.jpg
