clawdbotatg/clawd-pico-case/measurements/2026-09-24-cal-PINK-A1-stack-glass-to-pcb-back-1.jpg

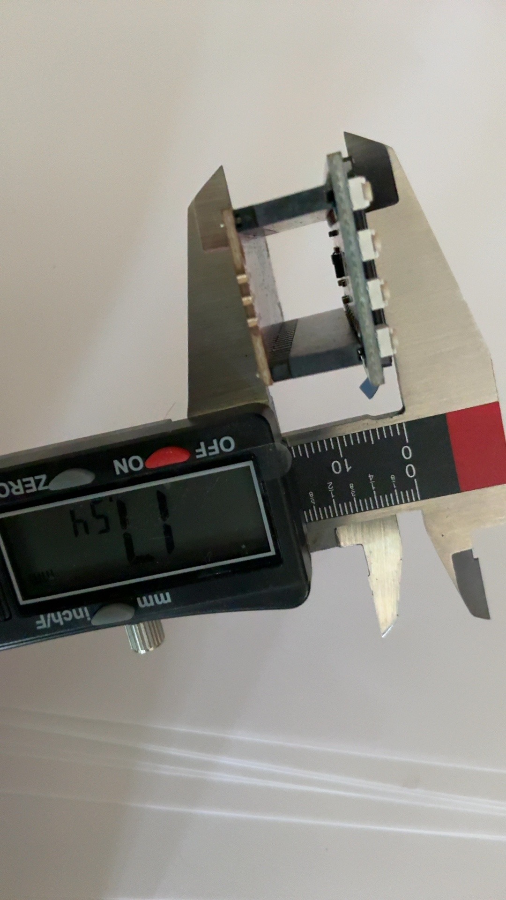
measurements/2026-09-24-cal-PINK-A1-stack-glass-to-pcb-back-1.jpg
