clawdbotatg/clawd-pico-case/measurements/2026-09-24-cal-PINK-P12-usbc-width-1.jpg

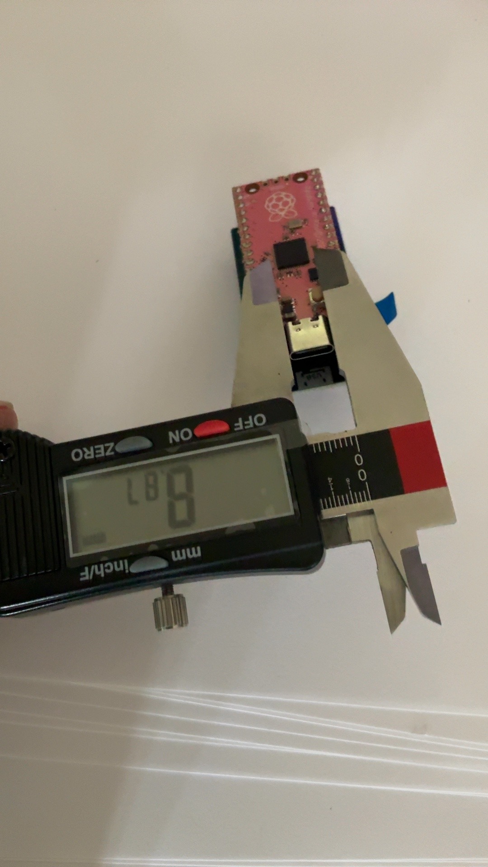
measurements/2026-09-24-cal-PINK-P12-usbc-width-1.jpg
