clawdbotatg/clawd-pico-case/measurements/2026-09-24-cal-PINK-P13-usbc-height-1.jpg

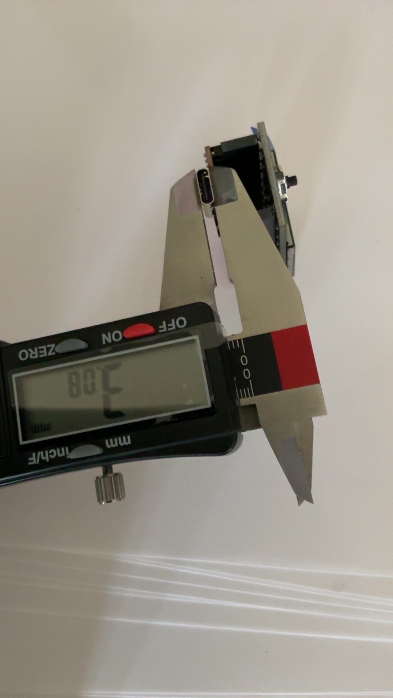
measurements/2026-09-24-cal-PINK-P13-usbc-height-1.jpg
