clawdbotatg/clawd-pico-case/measurements/2026-09-24-cal-PINK-P15-board-plus-usbc-height-1.jpg

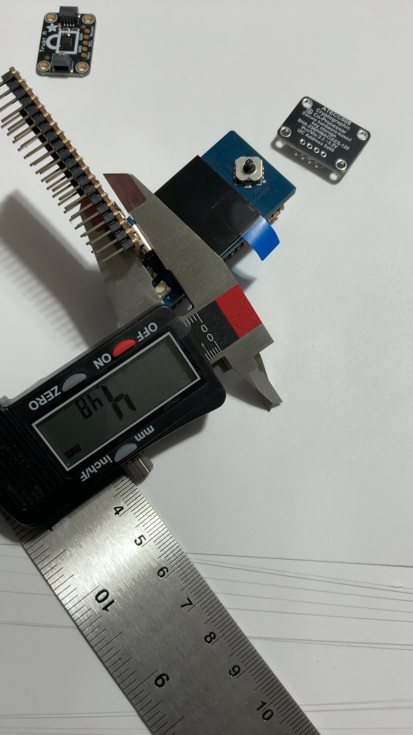
measurements/2026-09-24-cal-PINK-P15-board-plus-usbc-height-1.jpg
