clawdbotatg/clawd-pico-case/measurements/2026-09-24-cal-PINK-P18-pin-length-1.jpg

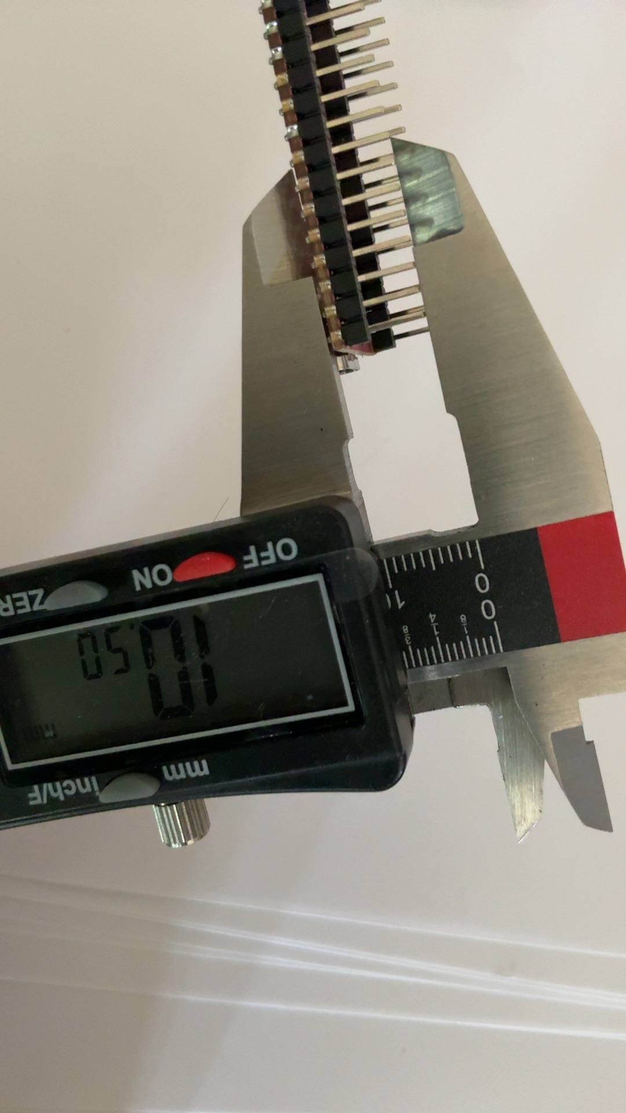
measurements/2026-09-24-cal-PINK-P18-pin-length-1.jpg
