clawdbotatg/clawd-pico-case/measurements/2026-09-24-cal-S3-lcd-glass-height-1.jpg

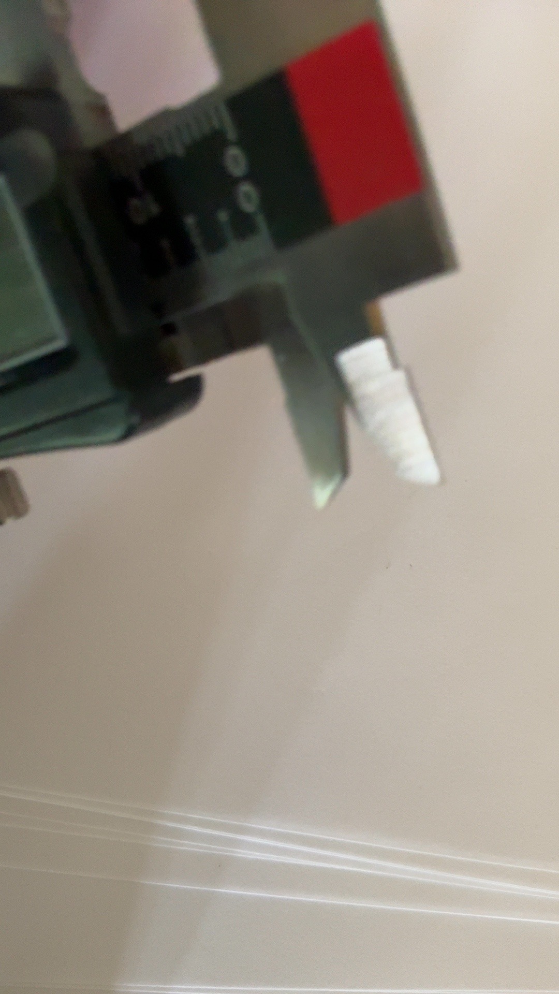
measurements/2026-09-24-cal-S3-lcd-glass-height-1.jpg
