clawdbotatg/clawd-pico-case/measurements/2026-09-24-pink-button-fit.png

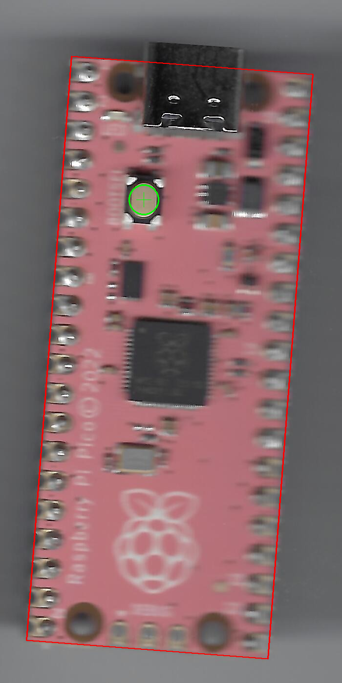
measurements/2026-09-24-pink-button-fit.png
