clawdbotatg/clawd-pico-case/measurements/2026-09-24-scan-01-all-boards-600dpi.jpg

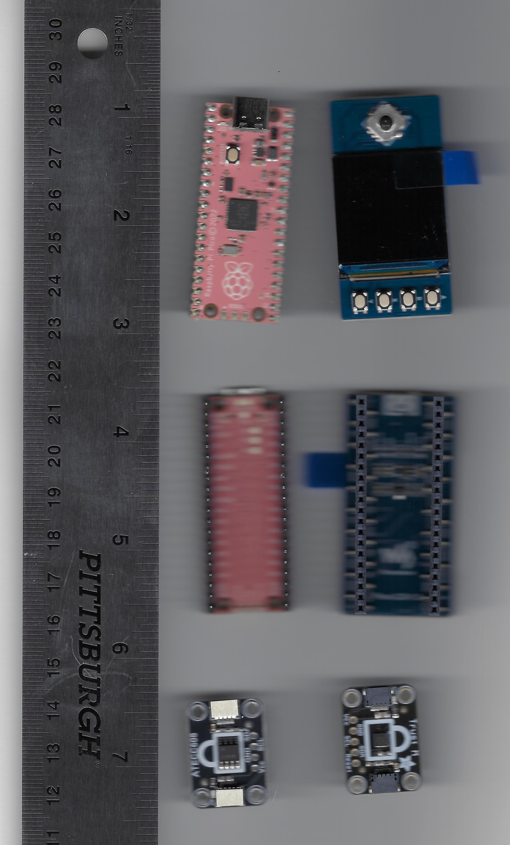
measurements/2026-09-24-scan-01-all-boards-600dpi.jpg
