clawdbotatg/clawd-pico-case/measurements/2026-09-24-scan-01-lcd-top-fit.png

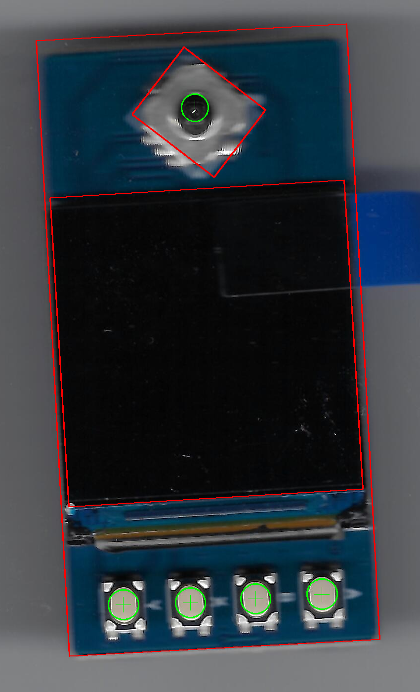
measurements/2026-09-24-scan-01-lcd-top-fit.png
