clawdbotatg/clawd-pico-case/measurements/2026-10-08-cal-RP2040PLUS-battery-plug-width-1.jpg

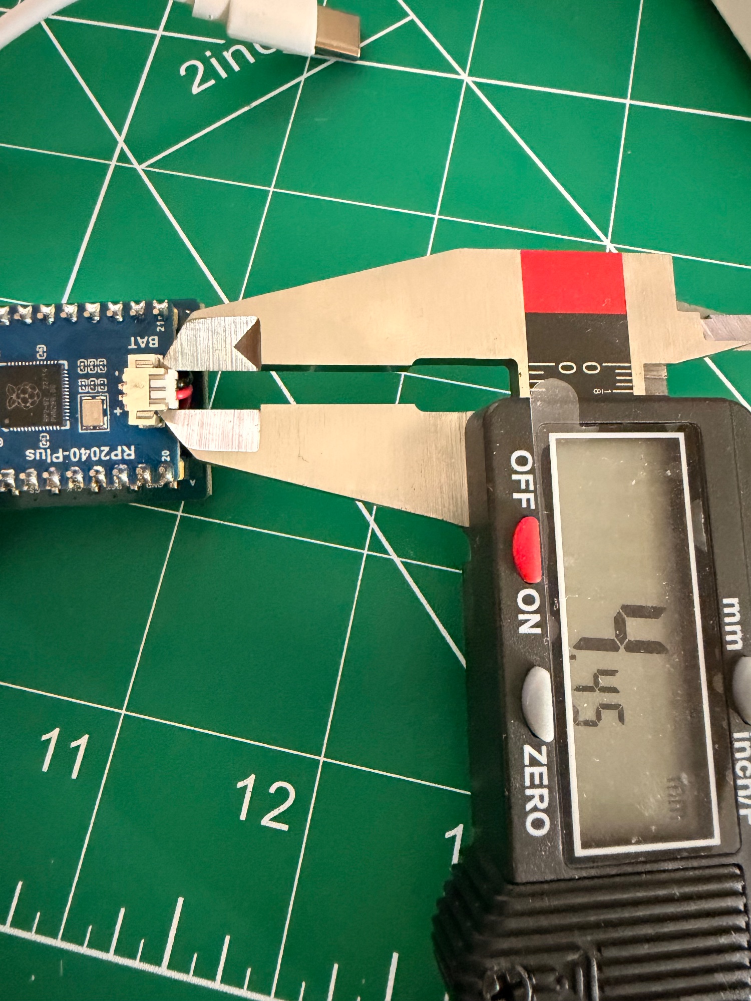
measurements/2026-10-08-cal-RP2040PLUS-battery-plug-width-1.jpg
