clawdbotatg/clawd-pico-case/measurements/2026-10-08-RP2040PLUS-reset-switch-side-1.jpg

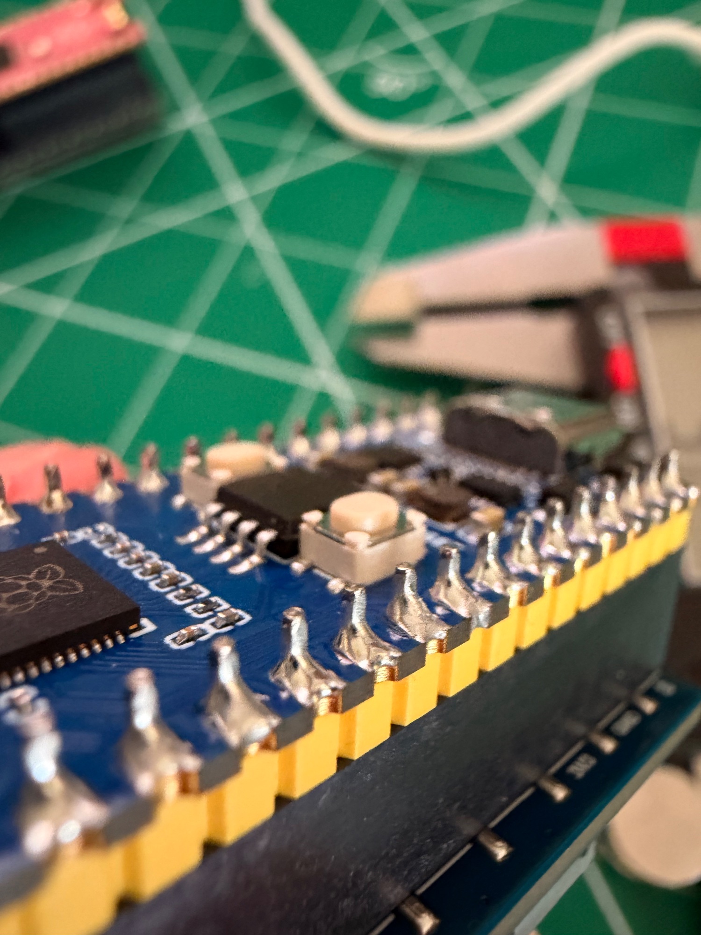
measurements/2026-10-08-RP2040PLUS-reset-switch-side-1.jpg
